bsikar/ra8p1-ereader-kicad/design/core_bulk_c9.md

# C9 core-regulator bulk capacitor

CORE-C9-001, 2026-09-27. C9 remains 47uF on MCU_VCORE with
Procurement_Status HOLD. A candidate is now recorded in its native KiCad
Selection_Basis and Sourcing_Snapshot fields. It is not yet promoted to
the canonical manufacturer part number or purchase BOM.

Candidate: **Murata GRM32ER71A476KE15K**. The manufacturer's
[GRM32ER71A476KE15-04CA reference sheet, January 10, 2025](https://search.murata.co.jp/Ceramy/image/img/A01X/G101/ENG/GRM32ER71A476KE15-04CA.pdf)
specifies 47uF +/-10%, 10V, X7R, -55..125C and 1210 size.
Body dimensions are 3.2 +/-0.3 by 2.5 +/-0.2 by 2.5 +/-0.2mm.
K is the 4000-piece reel packaging code; L is the 1000-piece reel code
for this same manufacturer control code. This does not establish electrical
equivalence to the older 6.3V E20 reference component.

[DigiKey candidate page](https://www.digikey.com/en/products/detail/murata-electronics/GRM32ER71A476KE15K/16034240),
observed 2026-09-27: Active, 1595 unreserved, 17-week standard lead time,
USD0.98 at quantity 1 and USD0.43690 at quantity 100. Cut-tape ordering
code is 490-GRM32ER71A476KE15KCT-ND. An earlier search result showed
13123; the opened page's 1595 supersedes that indexed count. Stock and
price are observations, not reservation or manufacturer lifecycle guarantees.

Historical hold: on 2026-09-05 the native field recorded Mouser stock7034
and an End of Life flag for GRM32ER70J476KE20L, conflicting with DigiKey's
indexed Active/zero-stock result. Do not erase this history by presenting
the E15 candidate as a renamed E20 part.

Initial-tolerance arithmetic is 47*(1-0.10)=42.3uF and
47*(1+0.10)=51.7uF. These are measurement-condition endpoints, not
guaranteed effective capacitance at the core voltage. The X7R temperature
classification alone does not establish a combined DC-bias, aging and
temperature bound.

Before final selection, compare manufacturer DC-bias/impedance data against
the actual RA8P1 core-voltage range and the allowed output network in the
Renesas hardware manual. Verify L1, the twelve 220nF local bypasses and C9
as one regulator output network, including startup and transients. A higher
voltage rating by itself is not proof of loop compatibility. Obtain the
applicable manufacturer approval specification before procurement.

This pass changes hidden metadata only; value, connectivity, drawing and
the existing purchase hold remain unchanged. The main-rail inventory must
continue to identify C9's canonical MPN as unspecified until selection is
approved electrically.

## CORE-C9-002: regulator acceptance evidence (2026-10-04)

Re-read RA8P1 HUM R01UH1064EJ0130 Rev.1.30, pages 4042-4044 and
4047, using the manufacturer's downloaded manual. Table 69.2 / Figure
69.1 establish the 2.2uH and 47uF output topology, twelve local 220nF
bypasses, and C9 return to VSS_DCDC. Section 69.3 recommends inductor
DCR at most 100mOhm. These passages do not state a numeric capacitor
ESR window or a minimum effective output capacitance. Do not invent
such limits or treat the nominal 47uF as an effective-capacitance floor.

Table 70.2 gives typical DCDC core targets of 0.950/0.925V in high-speed
mode and 0.950/0.925/0.825/0.765/0.715V in software standby. Its DCDC
rows have no min/max entries. The 0.92..0.99V external-VDD range and
1.2V absolute maximum are not substituted for a DCDC output guarantee.

Murata's [manufacturer product page](https://www.murata.com/en-eu/products/productdetail?partno=GRM32ER71A476KE15L)
identifies E15 L/K packing variants and the same 47uF, 10V X7R family.
This supports candidate identity; it does not establish regulator acceptance.
The previously linked detailed PDF returned HTTP 404 during this check;
no new DC-bias/impedance bound was obtained. C9 remains HOLD with no
canonical purchase MPN. Next evidence needed is current manufacturer
characterization and a Renesas-supported replacement acceptance criterion,
followed by output-network startup/transient validation.

This evidence update changes no CAD or BOM. The saved 14-page PDF and
97-error/11-warning ERC checkpoint remain applicable.
