bsikar/ra8p1-ereader-kicad/design/ereader_requirements.md

# E-reader hardware requirements

**Owner update, 2026-10-05:** PCM768/DSD512, premium Bluetooth audio and the
higher desktop output targets are now required. The authoritative new
[target contract and corrective plan](audio_external_review_2026-10-05.md#owner-adopted-target-contract)
supersedes the older optional-format, 2 W floor / 4 W stretch and 16 Vrms
language below. RA8P1 remains the application/system master. The existing
schematic does not yet implement these requirements; exact components,
continuous thermal capability and codec licenses remain engineering gates.

## Product definition

The owner's 2026-10-04 premium portable/desktop audio requirements are
tracked in [audio Stage 1 requirements](audio_stage1_requirements.md).
Network music comes from the owner's server; hardware resources/interfaces
are in scope, commercial streaming-service integration is not required.
Prior audio part choices remain provisional until the staged study closes.

Design a standalone RA8P1 e-reader using the existing `ereader/` KiCad project.
Integrate the e-paper timing controller, display power supplies, system power
management, and front-light driver on the main PCB. The Waveshare IT8951 HAT
is a prototyping reference, not a module in the finished product.

The following requirements were confirmed on 2026-09-05:

- Renesas RA8P1 host processor. The exact ordering code and package must be
  verified against the manufacturer's documentation before pin assignment.
- Capacitive touch input and physical buttons.
- Front light with independently adjustable warm and cool channels.
- A complete schematic and PCB design, developed and checked section by
  section, followed by whole-board integration and manufacturing checks.
- E-reader scope only. The Gaggia controller is a separate future project.

The active milestone is the complete electrical schematic, including readable
hierarchical sheets, qualified symbol pin mappings, ERC review, and a full
schematic PDF. PCB layout, footprint qualification, manufacturing outputs,
and physical bring-up are deferred; they are not schematic acceptance gates.

## Consolidated owner requirements (2026-09-07)

These requirements extend the original e-reader definition; they are not
optional substitutes for the display, touch, or front light. This is also a
portable music player. Unchecked items below are required work, not claims
that the current schematic implements them.

- [ ] RA8P1 host and ESP32-C6 radio, with complete supply, clock, reset,
  boot, programming, interconnect, and powered-off isolation circuits.
- [ ] Integrated e-paper controller, panel high-voltage power and VCOM,
  capacitive touch, and independently adjustable warm/cool front light.
  The Waveshare driver board is for prototyping only.
- [ ] Rechargeable battery, USB-C, charging and power-path management,
  protection, fuel measurement, safe power sequencing, and discharge.
- [ ] External RAM and soldered onboard storage at least matching the
  EK-RA8P1 baseline. The current reference is 64 MiB SDRAM and 64 MiB NOR;
  capacity alone does not establish equivalent bandwidth or compatibility.
- [ ] microSD for local music/files, with exact host interface, voltage,
  card-detect, protection, and repository-example compatibility checked.
- [ ] Premium headphone audio with both 3.5 mm single-ended and 4.4 mm
  balanced outputs, USB-DAC operation, and local-file playback.
  Define measurable noise, distortion, output impedance, load/power range,
  clocking, protection, and thermal requirements. Universal headphone
  compatibility or an unmeasured "best sound" claim is not acceptance.
- [ ] Built-in speakers and their amplifiers, with safe output selection,
  mute/pop suppression, and a complete battery/thermal budget.
- [ ] Two cameras: front-facing for selfies and possible face authentication,
  and rear-facing for photography. Use separate MIPI CSI-to-VIN and parallel
  CEU paths after complete pinmux, clock, bandwidth and power review.
- [ ] Independently controlled front camera illumination and rear flashlight,
  separate from the warm/cool display front light.
- [ ] Water-resistant product architecture, including USB-C moisture detection
  and wet-port power inhibition, with protection for exposed contacts.
- [ ] Five exposed physical buttons as specified below, plus touch input.
- [ ] Sensors, debug and factory recovery, including recovery when normal
  application firmware is unavailable.

### Owner additions (2026-09-13)

The owner requires two cameras and identified the MCU's two-lane MIPI
CSI-to-VIN path and separate 16-bit-capable parallel CEU as the intended
interfaces. An 8-bit parallel sensor remains possible; the peripheral's
maximum bus width does not specify the required sensor width. Verify actual
package pin availability and system bandwidth before promising concurrent
capture. Preserve all five buttons, premium audio, SDRAM, NOR and microSD
while resolving camera pin conflicts; existing reservations may be revised
only with coordinated interface review.

Provide a front-facing camera for selfies and possible face authentication,
with independently adjustable front-facing illumination, and a rear camera
with flashlight capability. Visible selfie illumination is the current
working basis. Infrared/depth sensing and spoof-resistant authentication
remain an investigation, not an implemented or guaranteed Face ID equivalent.
Define separate continuous torch and pulsed flash current/thermal limits,
hardware default-off behavior, and source transient budgets. These lights
do not replace either warm or cool display-frontlight control.

The rechargeable battery and the previously identified Waveshare-based
e-paper setup remain mandatory. The existing integrated-controller direction
is unchanged: the HAT is the prototype reference. The exact purchased panel
assembly and the ED060KHE candidate must not be treated as interchangeable
without matching electrical, touch, light-guide and waveform evidence.

Water resistance is a product requirement even while enclosure and PCB
implementation are deferred. Select connectors and electrical protection
with a sealable enclosure, exposed-contact corrosion and liquid ingress in
mind. USB-C requires moisture detection and a hardware-enforced safe state
that inhibits charging and VBUS sourcing while wet, with a defined dry-port
recovery policy. Review detection coverage, false indications, leakage,
power-off behavior, externally supplied VBUS, and interaction with CC/PD,
USB data and accessory functions before selecting the port controller and
switches. Moisture detection alone does not protect every exposed contact.
Include both headphone jacks, buttons and camera/service interfaces in the
ingress and corrosion review while retaining their required functionality.
No IP rating or immersion tolerance is claimed without an enclosure-level
test definition and physical qualification; water resistance is not an
electrical permission to operate or charge a wet connector.

### Five exposed buttons and recovery contract

The owner specified five buttons total on 2026-09-07. Allocate them as:

| Control | Required role |
| --- | --- |
| Power/wake | Power-on from off; wake/sleep request; orderly shutdown request; firmware-independent held-button forced off/recovery |
| Previous page | Page backward |
| Next page | Page forward |
| Volume down | Decrease audio volume |
| Volume up | Increase audio volume |

This count is one power button, two page buttons, and two dedicated volume
buttons. Do not silently collapse the latter four into two dual-use buttons.
Firmware may add contextual mappings, but the five physical controls remain.
For each, define debounce, ESD, pull defaults, voltage domain, leakage,
simultaneous-key behavior, and operation in off/boot/run/sleep/fault/update.
Reserve real MCU pins and verify wake-capable pin selection against the
selected sleep mode before completing the sheet.

The power button consolidates user-facing power/reset/recovery interaction;
it does not directly short both processors' unrelated boot-mode nets.
Normal startup is hardware controlled. A short press while powered is a
firmware input; a sustained press must ultimately force power off without
working firmware. Release and press again to restart. The exact forced-off
time, rail discharge, brownout/rearm behavior, and deep-sleep wake path require
electrical closure; a nominal timing calculation is not a guaranteed bound.

RA8P1 reset/boot and ESP32 boot service-pad pairs are internal fixture access,
not additional exposed buttons or fitted switches. Keep SWD and documented
ROM-loader access for blank/corrupt firmware. Any optional user-facing
button chord for a recovery UI is a separate firmware contract; do not claim
it substitutes for a proven hardware programming path.

### Execution and acceptance plan

Track the work in epic #821 and subsystem issues #822-#834, #840 (audio),
and #841 (camera). Issues #835-#838 cover deferred PCB/manufacturing stages.
Power and controls are shared work under #825/#832; memory, onboard storage
and microSD are under #827. Reopen interface and power-budget decisions when
the expanded audio/camera load invalidates earlier allocations.

1. Complete and independently review each electrical section and its exact
   symbol pin mapping; keep the BOM synchronized with placed parts.
2. Select viable parts using primary datasheets and dated DigiKey/Mouser
   stock, price, lifecycle, and performance evidence. Flag unqualified
   candidates and unavailable supporting specifications explicitly.
3. Connect hierarchical interfaces and actual MCU pins, including all rail,
   timing, pinmux, powered-off, recovery, and firmware dependencies.
4. Put useful equations, assumptions, results, and stable calculation IDs
   on the schematic and link them to full engineering documents. Verify
   calculations with Python; distinguish estimates from guaranteed limits.
5. Before each commit/push, review connectivity, pin types, ERC findings,
   calculations, BOM, and the native schematic plus every changed PDF page.
   Existing ERC errors are not a passing full-design gate.
6. Export the full multipage schematic PDF with the export script. Version
   editable project files, local libraries, necessary references, BOM,
   engineering documents, and exports using portable project-relative paths.
7. Complete whole-design review under #834 before claiming schematic done.
   PCB layout and footprint/model qualification remain deferred.

Latest owner direction is native KiCad GUI editing for design work. Scripts
are for exports and permitted supporting calculations/imports, not schematic
generation. Parallel agents research and independently review while one
editor owns the live KiCad design. Maintain compact, consistent symbols,
short clear wiring, readable hierarchy, standard power symbols, and honest
ERC drive semantics; do not add power flags merely to hide real errors.

Supporting engineering documents: [power](system_power_design.md),
[power button](single_button_power.md), [service](service_interface.md),
[audio](audio_subsystem.md), and
[camera/storage/memory](camera_storage_interfaces.md).

### Component selection and procurement acceptance

Owner requirement, October 5, 2026: apply these checks to every placed part
and to every future selection, including passives and purchased modules.

1. Verify the exact ordering code against manufacturer lifecycle information.
   Reject NRND/EOL choices for new design unless the owner explicitly accepts
   an exception. Record PCNs, replacement codes and any published longevity
   commitment with its scope and end date. Active status alone cannot promise
   that a component will not become obsolete soon.
2. Find an authorized, in-stock quantity-one offer. Record supplier, ordering
   code, carrier choice, minimum/multiple, price, stock quantity and evidence
   date/age. Stock must cover the number fitted to one board. Factory reel
   size is not a distributor cut-tape minimum; avoid optional reeling fees.
   Cached stock, backorder prices and failed page retrievals cannot pass a
   live procurement check.
3. Justify electrical fit for each use and compare realistic alternatives.
   Include voltage/current/temperature limits, timing, noise, tolerances,
   startup, shutdown, partial-power behavior and fault conditions as relevant.
   Matching pin numbers or a distributor's substitute label does not qualify
   a replacement circuit.
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
