bsikar/ra8p1-ereader-kicad/resources/manuals/Renesas_EK-RA8D2_Board_BOM.xlsx

 |  | Bill of Materials
 |  | d019762
 | Document Number | d019762_02
 | Project Name | EK-RA8D2
 | Variant | customer
 | Version | 0303
 | Date | 18/11/2025
Line # | Part Number | Value | Designator | Description | Quantity | Fitted | Remarks | Manufacturer | Manufacturer Part Number
 | ACS-00000005 |  | ACS5, ACS6, ACS7, ACS8 | Pan Phillips Screw, M3x0p5, Length 6mm, Natural, Nylon | 4 | Fitted |  | Essentra | 50M030050P006
 | ICS-00000034 |  | U6, U9, U19 | Bus Driver, 4-Func, 1-Bit, True Output, CMOS, DHVQN14, SOT762-1 | 3 | Fitted |  | Nexperia | 74CBTLV3126BQ,115
 | ICS-00000017 |  | U5, U12, U13, U22, U23, U24, U25 | Octal FET Bus Switch, 5 ohm, 0.3ns max delay, DHVQFN20 | 7 | Fitted |  | Nexperia | 74CBTLV3245BQ-Q10X
 | MIS-00003478 | TP | TP1, TP2, TP3, TP4, TP7, TP8, TP9, TP10 | Testpoint Miniature SMD 3.81mmx2.03mm | 8 | Fitted |  | Keystone | 5019
 | CON-00000063 |  | J41 | Header,4way,2row,vertical,2mm,SMD | 1 | Fitted |  | Amphenol Communications Solutions | 57202-G52-02ALF
 | CON-00000093 |  | J1 | Header,40way,2row,vertical,2.54mm,SMT | 1 | Fitted |  | Amphenol Communications Solutions | 95157-240LF
 | DIO-00000012 |  | LED1 | Standard LEDs - SMD Blue, 470nm 90 to 145 mcd | 1 | Fitted |  | Wurth Elektronik | 150060BS75000
 | DIO-00000013 |  | LED2 | Standard LEDs - SMD Green, 525nm 220 to 430 mcd | 1 | Fitted |  | Wurth Elektronik | 150060GS75000
 | DIO-00000014 |  | LED3 | Standard LEDs - SMD Red, 625nm 120 to 250 mcd | 1 | Fitted |  | Wurth Elektronik | 150060RS75000
 | DIO-00000015 |  | LED5, LED7 | Standard LEDs - SMD Yellow, 590nm 90 to 120 mcd | 2 | Fitted |  | Wurth Elektronik | 150060YS75000
 | CON-00000066 |  | J35 | FFC/FPC Connector, 40 Contact(s), 1 Row(s), Female, Right Angle, 0.019 inch Pitch, Surface Mount Terminal, Locking, Beige Insulator | 1 | Fitted |  | Molex | 505110-4091
 | CON-00000097 |  | J6, J8, J9, J16 | Header, 3way, 1row, vertical, 2.00mm, SMD | 4 | Fitted |  | TE Connectivity | 2842102-3
 | CON-00000065 |  | J7, J10, J11 | Connector USB 3.2 Gen2 Type C Horizontal SMD | 3 | Fitted |  | Amphenol Commercial | 12401610E4#2A
 | CON-00000062 |  | J27, J28 | Grove Header,4Way,1 Row, Horizontal,2mm,THT | 0 | Not Fitted |  | Seeed Studio | 110990037
 | CON-00000088 |  | J15 | 10/100/1000 Ethernet Jack, RJ45, Right Angle SMT, No LEDs | 1 | Fitted |  | Wurth Elektronik | 7498111001A
 | CON-00003283 |  | J33, J34, J36, J60 | Header,2way,1row,vertical,2.54mm,THT | 0 | Not Fitted |  | Wurth Elektronik | 61300211121
 | CON-00003286 |  | J31 | Header,5way,1row,vertical,2.54mm,THT | 0 | Not Fitted |  | Wurth Elektronik | 61300511121
 | CON-00003301 |  | J4, J17 | Header,20way,2row,vertical,2.54mm,THT | 0 | Not Fitted |  | Wurth Elektronik | 61302021121
 | CON-00003310 |  | J2, J3 | Header,40way,2row,vertical,2.54mm,THT | 0 | Not Fitted |  | Wurth Elektronik | 61304021121
 | CON-00000115 |  | J38 | Header,20way,2row,vertical,2.00mm,THT | 0 | Not Fitted |  | Wurth Elektronik | 62002021121
 | MEC-00003402 |  | SW4 | WS-DISV Small Compact SMT Flat Actuator with Top Tape 1.27 mm | 1 | Fitted |  | Wurth Elektronik | 416131160808
 | CRY-00000004 | 32.768kHz | X2 | Crystal, 32.768kHz, 12.5pF, 3.2x1.5 | 1 | Fitted |  | Abracon | ABS07-32.768KHZ-1-T
 | DIO-00000007 |  | D3, D4, D6, D14 | Rectifier Diode, Schottky, 1 Phase, 1 Element, 3A, 40V V(RRM), Silicon | 4 | Fitted |  | Diodes Inc. | B340AQ-13-F
 | IND-00000002 | 4.7µH | L1 | Power Inductor Shielded Multilayer 4.7uH 20% 3MHz Ferrite 700mA | 1 | Fitted |  | Pulse Electronics | BKPB002012104R7MA2
 | CAP-00003477 | 27pF | C22, C23 | Capacitor,EIA0402,27p,50V,C0G | 2 | Fitted |  | Yageo Group | CC0402JRNPO9BN270
 | CON-00000111 |  | J21, J22 | Socket,8way,1row,vertical,2.54mm,THT | 0 | Not Fitted |  | Samtec | CES-108-01-T-S
 | ICS-00000019 |  | U14 | Ultra-Low Power Stereo Codec | 1 | Fitted |  | Renesas | DA7212-01UM2
 | IND-00000004 | 90 | FL1, FL2 | Common Mode Choke / Filters, 90uH 25%, 0.1A, 3.8Ohm DCR | 2 | Fitted |  | Murata | DLM0NSM900HY2D
 | CRY-00000002 | 12MHz | X3 | Crystal, 12.000MHz, 10 pF, 2.5x2 | 1 | Fitted |  | ECS International | ECS-120-10-36B-CWY-TR
 | CRY-00000003 | 25MHz | X4 | Crystal, 25.000MHz, 10 pF, 2x1.6 | 1 | Fitted |  | ECS International | ECS-250-10-37B-CTN-TR
 | CON-00003434 |  | J32 | Edge Rate Rugged High Speed Socket/Terminal Strip | 1 | Fitted |  | Samtec | ERF8-013-05.0-L-DV-TR
 | RES-00003205 | 10m | R7, R98 | Resistor,EIA0603,10m,0.25W | 2 | Fitted |  | Panasonic | ERJ-3LWFR010V
 | RES-00003215 | 1k | RA21 | Array/Network Resistor, Isolated, Metal Glaze/thick Film, 0.063W, 1000ohm, 25V, 5% +/-Tol, 200ppm/Cel, Surface Mount, 1506 | 1 | Fitted |  | Panasonic | EXB-2HV102JV
 | RES-00003208 | 10k | RA1, RA20 | Resistor Network & Array,EIA1506,10k,0.063W | 2 | Fitted |  | Panasonic | EXB-2HV103JV
 | CRY-00000005 | 24MHz | X1 | Crystal, 24MHz, 10pF, 3.2x2.5 | 1 | Fitted |  | Diodes Inc. | FL2400022
 | CON-00000113 |  | J13 | Header,10way,2row,vertical,1.27mm,SMD | 1 | Fitted |  | Samtec | FTSH-105-01-F-DV-K-TR
 | CON-00000114 |  | J20 | Header,20way,2row,vertical,1.27mm,SMD,gold flash on post | 1 | Fitted |  | Samtec | FTSH-110-01-F-DV-K-TR
 | CAP-00000010 | 100nF | C128, C129 | Capacitor,EIA1206,100n,100V,C0G | 2 | Fitted |  | Murata | GCM31C5C2A104JE02L
 | CAP-00003207 | 22µF | C82 | Capacitor,EIA1206,22u,10V,X7R | 1 | Fitted |  | Murata | GCM31CR71A226KE02L
 | CAP-00003208 | 220nF | C50, C52, C53, C54, C55, C58, C59, C63, C73, C74, C75, C76, C99 | Capacitor,EIA0402,220n,16V,X7R | 13 | Fitted |  | Murata | GCM155R71C224KE02D
 | CAP-00003212 | 10nF | C29, C87, C89, C92, C97, C98, C101, C102, C103, C104, C105 | Capacitor,EIA0402,10n,50V,X7R | 11 | Fitted |  | Murata | GCM155R71H103KA55D
 | CAP-00000002 | 330pF | C142 | Capacitor,EIA0402,330p,100V,X7R | 1 | Fitted |  | Murata | GCM155R72A331KA37D
 | CAP-00000012 | 15pF | C21, C24 | Capacitor,EIA0201,15p,50V,C0G | 2 | Fitted |  | Murata | GCM0335C1H150FA16D
 | CAP-00003371 | 47µF | C77 | Capacitor,EIA1206,47u,6.3V,X7U | 1 | Fitted |  | Murata | GRM31CE70J476ME15L
 | CAP-00003447 | 10µF | C20, C34, C64, C65, C79, C88, C90, C100, C106, C115, C149 | Capacitor,EIA0402,10u,10V,X5R | 11 | Fitted |  | Murata | GRM155R61A106ME11D
 | CAP-00003447 | 10µF | C162 | Capacitor,EIA0402,10u,10V,X5R | 0 | Not Fitted |  | Murata | GRM155R61A106ME11D
 | CAP-00000013 | 22µF | C141 | Capacitor,EIA0402,22u,10V,X5R | 1 | Fitted |  | Murata | GRM158R61A226ME15D
 | CAP-00000011 | 1µF | C130, C131, C132, C133, C134, C135, C136, C137, C138 | Capacitor,EA0201,1u,10V,X6S | 9 | Fitted |  | Murata | GRT033C81A105ME13D
 | CAP-00000011 | 1µF | C143, C144, C145, C146, C147 | Capacitor,EA0201,1u,10V,X6S | 0 | Not Fitted |  | Murata | GRT033C81A105ME13D
 | CAP-00000015 | 2.2µF | C10, C83 | Capacitor,EIA0402,2.2u,16V,X6S | 2 | Fitted |  | Murata | GRT155C81C225KE13D
 | CAP-00000014 | 1µF | C18, C30, C60, C66, C110, C114, C152, C154 | Capacitor,EIA0402,1u,25V,X6S | 8 | Fitted |  | Murata | GRT155C81E105KE13D
 | CAP-00003217 | 470nF | C68 | Capacitor,EIA0402,470n,10V,X7R | 1 | Fitted |  | Murata | GRT155R71A474KE01D
 | CAP-00003203 | 100nF | C1, C2, C3, C4, C5, C6, C7, C8, C9, C11, C12, C13, C14, C15, C16, C17, C19, C25, C26, C28, C31, C32, C33, C35, C36, C37, C39, C40, C41, C42, C43, C44, C45, C46, C47, C48, C49, C51, C56, C57, C61, C67, C71, C72, C78, C80, C81, C84, C85, C91, C93, C94, C107, C109, C111, C112, C113, C116, C117, C118, C121, C122, C123, C124, C125, C126, C127, C140, C148, C151, C155, C156, C157, C158, C159, C160 | Capacitor,EIA0402,100n,50V,X7R | 76 | Fitted |  | Murata | GRT155R71H104KE01D
 | CAP-00003203 | 100nF | C108, C139 | Capacitor,EIA0402,100n,50V,X7R | 0 | Not Fitted |  | Murata | GRT155R71H104KE01D
 | CAP-00003210 | 4.7µF | C27, C69, C70, C153 | Capacitor,EIA0603,4.7u,16V,X7S | 4 | Fitted |  | Murata | GRT188C71C475KE13D
 | CAP-00003215 | 10pF | C95, C96, C119, C120 | Capacitor,EIA0402,10p,100V,C0G | 4 | Fitted |  | Murata | GRT1555C2A100JA02D
 | CAP-00003209 | 47pF | C62 | Capacitor,EIA0402,47p,100V,C0G | 1 | Fitted |  | Murata | GRT1555C2A470JA02D
 | TRA-00000004 |  | Q10, Q18 | N-Channel 30V 5A 1.3W MOSFET | 2 | Fitted |  | Infineon | IRLML6344TRPBF
 | ICS-00000135 |  | U3 | NOR Flash 512Mb, Octal Flash, 3V, 24-ball TFBGA | 1 | Fitted |  | ISSI | IS25LX512M-JHLE
 | ICS-00000024 |  | U2 | 512Mb Synchronous DRAM, 16MX32, 5.4ns, CMOS, TF-BGA90 | 1 | Fitted |  | ISSI | IS42S32160F-6BLI
 | ICS-00000140 |  | U52 | LDO with Low ISUPPLY, High PSRR 1.8V fixed, 300mA | 1 | Fitted |  | Renesas | ISL9005AIRCZ-T
 | ICS-00000015 |  | U16, U17 | Single, General Purpose Micropower, RRIO Operational Amplifier | 2 | Fitted |  | Renesas | ISL28113FEZ-T7
 | ICS-00000014 |  | U8 | High Performance 3A Linear Regulator | 1 | Fitted |  | Renesas | ISL80103IRAJZ
 | CAP-00000022 | 4.7µF | C38, C150 | Capacitor, EIA0402, 4.7u, 16V, X5R | 2 | Fitted |  | KYOCERA AVX | KGM05CR51C475MH
 | DIO-00003239 |  | LED8 | Standard LEDs - SMD Green, 570nm 2.2 to 5.6 mcd | 1 | Fitted |  | Osram | LGL29K-G2J1-24
 | DIO-00003241 |  | LED6 | Standard LEDs - SMD Orange, 606nm 3.55 to 14 mcd | 1 | Fitted |  | Osram Opto | LOL29K-H2L1-24
 | DIO-00000002 |  | LED4 | Standard LEDs, SMD Ultra Bright White | 1 | Fitted |  | Lite-On | LTW-C191DS5
 | IND-00000008 | 120 | L5 | Ferrite Chip, 1.2A, 90mOhm DCR, 120Ohm Impedance @100MHz | 1 | Fitted |  | TDK | MPZ1005S121CT000
 | ACS-00000000 |  | ACS1, ACS2, ACS3, ACS4 | Female Standoff; Nylon; Natural; M3; 14.0 mm Spacer | 4 | Fitted |  | Essentra | MTS-14
 | RES-00000000 | 100k | RT1, RT2 | NTC Thermistor, R_EIA0402, 100K, 4250K | 2 | Fitted |  | Murata | NCP15WF104F03RC
 | CON-00000043 |  | J19 | Socket, 6way, 1 Row, Vertical, 2.54mm, SMD | 1 | Fitted |  | Sullins | NPTC061KFXC-RC
 | CON-00000044 |  | J18, J23 | Socket, 8way, 1 Row, Vertical, 2.54mm, SMD | 2 | Fitted |  | Sullins | NPTC081KFXC-RC
 | CON-00000045 |  | J24 | Socket, 10way, 1 Row, Vertical, 2.54mm, SMD | 1 | Fitted |  | Sullins | NPTC101KFXC-RC
 | CON-00000078 |  | J5 | Header, 2way, 1row, vertical, 2.00mm, THT | 0 | Not Fitted |  | Sullins | NRPN021PAEN-RC
 | CON-00000079 |  | J12 | Header, 3way, 1row, vertical, 2.00mm, THT | 0 | Not Fitted |  | Sullins | NRPN031PAEN-RC
 | CON-00000105 |  | J29 | Header, 8way, 2row, vertical, 2.0mm, SMD | 1 | Fitted |  | Sullins | NRPN042MAMS-RC
 | CON-00000094 |  | J14, J37 | Header,26way,2row,vertical,2.00mm,THT | 0 | Not Fitted |  | Sullins | NRPN132PAEN-RC
 | ICS-00000025 |  | U11 | Ethernet Network Connection GPY111 Gigabit Ethernet (GbE) | 1 | Fitted |  | MaxLinear | PEF7071VV16-LLHU
 | ICS-00000012 |  | U15 | Low-voltage translating 8-bit I2C-bus I/O Expander | 1 | Fitted |  | Diodes Inc. | PI4IOE5V6408ZTAEX
 | RES-00003207 | 5m | R2, R3 | Current Sense Resistor,EIA0612,5m,1W | 2 | Fitted |  | Yageo Group | PS0612FKE070R005L
 | MEC-00000000 |  | SW3 | SMD Push Button Switch, 4-pin, 6x6mm, 4.3mm height, Red Actuator | 1 | Fitted |  | C&K Components | PTS645SK43SMTR92LFS
 | MEC-00000002 |  | SW1, SW2 | SMD Push Button Switch, 4-pin, 6x6mm, 4.3mm height, Blue Actuator | 2 | Fitted |  | C&K Components | PTS645SM43SMTR92LFS
 | ICS-00000006 |  | U7 | Renesas RA4M2 32-bit MCU, ARM Cortex-M33, 100MHz, 512kB Flash, 128 kB RAM, 48-pin LQFP package (used for J-Link onboard debug i/f) | 1 | Fitted |  | Renesas | R7FA4M2AD3CFL#AA0
 | ICS-00000098 |  | U1 | Renesas RA8D2 32-bit MCU, High-performance 1 GHz Arm® Cortex®-M85 core, 250 MHz Arm® Cortex®-M33 core, up to 1 MB code MRAM, and 2 MB SRAM with ECC | 1 | Fitted |  | Renesas | R7KA8D2KFLCAC
 | ICS-00000018 |  | U4, U18 | USB Power Delivery Controller, USB 3.1, HVQFN32 | 2 | Fitted |  | Renesas | R9A02G011GNP#AC0
 | DIO-00000005 |  | D15, D16 | Rectifier Diode, Schottky, 1 Phase, 1 Element, 1A, 40V V(RRM), Silicon | 2 | Fitted |  | ROHM | RB168MM-40TFTR
 | RES-00000882 | 1.5k | R37 | Resistor,EIA0402,1.5k,0.0625W | 1 | Fitted |  | Yageo Group | RC0402FR-071K5L
 | RES-00000878 | 1k | R24, R88, R122 | Resistor,EIA0402,1k,0.0625W | 3 | Fitted |  | Yageo Group | RC0402FR-071KL
 | RES-00001614 | 2.37k | R33, R34 | Resistor,EIA0402,2.37k,0.0625W | 2 | Fitted |  | Yageo Group | RC0402FR-072K37L
 | RES-00000886 | 2.2k | R80 | Resistor,EIA0402,2.2k,0.0625W | 1 | Fitted |  | Yageo Group | RC0402FR-072K2L
 | RES-00001635 | 3.92k | R41 | Resistor,EIA0402,3.92k,0.0625W | 1 | Fitted |  | Yageo Group | RC0402FR-073K92L
 | RES-00000894 | 4.7k | R11, R25, R26, R28, R38, R44, R54, R56, R83, R103, R109, R111 | Resistor,EIA0402,4.7k,0.0625W | 12 | Fitted |  | Yageo Group | RC0402FR-074K7L
 | RES-00001375 | 4.99 | R112 | Resistor,EIA0402,4.99,0.0625W | 1 | Fitted |  | Yageo Group | RC0402FR-074R99L
 | RES-00000895 | 5.1k | R12, R17, R48, R49, R89, R92 | Resistor,EIA0402,5.1k,0.0625W | 6 | Fitted |  | Yageo Group | RC0402FR-075K1L
 | RES-00000902 | 10k | R6, R14, R36, R39, R40, R45, R46, R47, R52, R71, R77, R94, R95, R99, R105, R107, R113, R119, R120, R121, R123, R136, R137, R138, R139 | Resistor,EIA0402,10k,0.0625W | 25 | Fitted |  | Yageo Group | RC0402FR-0710KL
 | RES-00000903 | 11k | R42, R43 | Resistor,EIA0402,11k,0.0625W | 2 | Fitted |  | Yageo Group | RC0402FR-0711KL
 | RES-00000906 | 15k | R4, R18, R76, R79, R90 | Resistor,EIA0402,15k,0.0625W | 5 | Fitted |  | Yageo Group | RC0402FR-0715KL
 | RES-00000834 | 15 | R1, R114, R115, R116 | Resistor,EIA0402,15,0.0625W | 4 | Fitted |  | Yageo Group | RC0402FR-0715RL
 | RES-00001689 | 16.2k | R8, R85 | Resistor,EIA0402,16.2k,0.0625W | 2 | Fitted |  | Yageo Group | RC0402FR-0716K2L
 | RES-00000907 | 16k | R50, R51 | Resistor,EIA0402,16k,0.0625W | 2 | Fitted |  | Yageo Group | RC0402FR-0716KL
 | RES-00000840 | 27 | R21, R22 | Resistor,EIA0402,27,0.0625W | 2 | Fitted |  | Yageo Group | RC0402FR-0727RL
 | RES-00000913 | 30k | R5, R15, R81, R91 | Resistor,EIA0402,30k,0.0625W | 4 | Fitted |  | Yageo Group | RC0402FR-0730KL
 | RES-00000842 | 33 | R59, R60, R61, R62, R63, R64 | Resistor,EIA0402,33,0.0625W | 6 | Fitted |  | Yageo Group | RC0402FR-0733RL
 | RES-00000843 | 36 | R125, R126 | Resistor,EIA0402,36,0.0625W | 2 | Fitted |  | Yageo Group | RC0402FR-0736RL
 | RES-00000918 | 47k | R31, R82, R102 | Resistor,EIA0402,47k,0.0625W | 3 | Fitted |  | Yageo Group | RC0402FR-0747KL
 | RES-00000926 | 100k | R10, R16, R55, R57, R69, R73, R84, R96, R97, R101, R104, R106, R110 | Resistor,EIA0402,100k,0.0625W | 13 | Fitted |  | Yageo Group | RC0402FR-07100KL
 | RES-00000855 | 110 | R32 | Resistor,EIA0402,110,0.0625W | 1 | Fitted |  | Yageo Group | RC0402FR-07110RL
 | RES-00000858 | 150 | R117, R118, R140 | Resistor,EIA0402,150,0.0625W | 3 | Fitted |  | Yageo Group | RC0402FR-07150RL
 | RES-00000867 | 360 | R124 | Resistor,EIA0402,360,0.0625W | 1 | Fitted |  | Yageo Group | RC0402FR-07360RL
 | RES-00000870 | 470 | R30, R35, R65 | Resistor,EIA0402,470,0.0625W | 3 | Fitted |  | Yageo Group | RC0402FR-07470RL
 | RES-00000801 | 0 | R13, R19, R20, R53, R67, R68, R78, R127, R128, R129, R130, R131, R132, R133, R134, R135 | Resistor,EIA0402,0,0.0625W | 16 | Fitted |  | Yageo Group | RC0402JR-070RL
 | RES-00000801 | 0 | R23, R66, R70, R74, R75, R87, R108 | Resistor,EIA0402,0,0.0625W | 0 | Not Fitted |  | Yageo Group | RC0402JR-070RL
 | RES-00002248 | 2.61k | R29 | Resistor,EIA0603,2.61k,0.1W | 1 | Fitted |  | Yageo Group | RC0603FR-072K61L
 | RES-00002182 | 464 | R27 | Resistor,EIA0603,464,0.1W | 1 | Fitted |  | Yageo Group | RC0603FR-07464RL
 | RES-00000804 | 0 | R9, R58, R86, R93 | Resistor,EIA1206,0,0.25W | 4 | Fitted |  | Yageo Group | RC1206JR-070RL
 | DIO-00003463 |  | D1, D2, D7, D8, D10, D11 | Low Capacitance TVS Diode Array | 6 | Fitted |  | Semtech | RCLAMP0582N.TCT
 | TRA-00000001 |  | Q2, Q3, Q4, Q12, Q21 | N-Channel 60V 250mA Small Signal MOSFET | 5 | Fitted |  | ROHM | RE1L002SNTL
 | RES-00003204 | 220 | R72, R100 | Resistor,EIA2512,220,1W | 2 | Fitted |  | Stackpole Electronics | RMCF2512FT220R
 | TRA-00000003 |  | Q1, Q11 | Dual P-Channel -12V -4.5A MOSFET | 2 | Fitted |  | Vishay | SIA975DJ-T1-GE3
 | ICS-00000194 |  | U10 | Renesas GreenPak PMOD mode controller | 1 | Fitted |  | Renesas | SLG7RN48896
 | CON-00000061 |  | J30 | Wire-to-Board Header,4way, Single Row, Right-Angle, SMD | 0 | Not Fitted |  | JST | SM04B-SRSS-TB(LF)(SN)
 | CON-00000060 |  | J25, J26 | Socket,12way,2row,horizontal,2.54mm,SMD,PMOD_Interface | 2 | Fitted |  | Samtec | SMH-106-02-L-D
 | ICS-00000021 |  | U20 | 4-Bit 1-of-2 FET Multiplexer/Demultiplexer 2.5-V/3.3-V Low-Voltage High-Bandwidth Bus Switch | 1 | Fitted |  | Texas Instruments | SN74CB3Q3257DBQR
 | ICS-00000023 |  | MIC1, MIC2 | Multimode Digital Bottom Port Silicon Digital Microphone with a single bit PDM output | 2 | Fitted |  | Knowles Acoustics | SPH0690LM4H-1
 | IND-00000003 | 2.2µH | L2 | Inductor, 2.2uH, 20%, 7A, Metal-Core | 1 | Fitted |  | TDK | SPM5020T-2R2M-LR
 | ICS-00000096 |  | U21 | 6-GHz, 5-V, 2: 1 (SPDT) 10-channel MIPI switch with 1.8-V logic support 36-NFBGA -40 to 85 | 1 | Fitted |  | Texas Instruments | TMUX646NZECR
 | DIO-00000001 |  | D5, D9, D12 | ESD Suppressor Diode TVS Uni-Dir 22V 55Vc Automotive 2-Pin SGP T/R | 3 | Fitted |  | Semtech | UCLAMP2271P.TNT
 | RES-00003456 | 4.7k | RA2, RA3, RA4, RA5, RA6, RA7, RA8, RA9, RA10 | Resistor Network & Array,0804,4.7k,0.0625W | 9 | Fitted |  | Yageo Group | YC124-FR-074K7L
 | RES-00003206 | 10k | RA11, RA12, RA13 | Resistor Network & Array,0804, 10k,0.0625W | 3 | Fitted |  | Yageo Group | YC124-FR-0710KL
 | RES-00003457 | 33 | RA14, RA15, RA16, RA17, RA18, RA19 | Resistor Network & Array,0804,33,0.0625W | 6 | Fitted |  | Yageo Group | YC124-FR-0733RL
 | RES-00003219 | 50 | RA22, RA23, RA24 | Resistor Network & Array,0804, 50,0.0625W | 3 | Fitted |  | Yageo Group | YC124-FR-0749R9L
