bsikar/ra8p1-ereader-kicad/resources/reference_designs/Renesas_EK-RA8D2_Board_Design_Package/Design Files - Altium/d019762_43_v0303_ek-ra8d2_altium_customer_mp/PCB_Tech_Spec.xlsx

Sheet: Technical data sheet
 | PCB Technology Specification
 |  | Field=DNumber
Field=Dnumber | Document Number | Field=Dnumber_07_S01
Field=ProjectName | Project Name | Field=Proj
 | Variant | Field=VariantName |  | Contact Person |  | Field=Engineer
 | Version | Field=ItemRevision |  | E-Mail |  | Field=Email
 | Date | Field=CurrentDate |  | Telephone |  | Field=Phone
 | General requirements |  |  |  | Production requirements
 | IPC-A-600 |  | Class II |  | PCB-Type |  | Rigid
 | IPC-A-6011/IPC-A-6012 |  | Class II |  | Finished PCB Dimension (mm) |  | 84 mm | x | 190 mm
 | Number of Layers |  | see drawing |  | Create Panel |  | no |  | 5 x 5
 | Conductor min Width / Spacing |  | 60 µm |  | Panel Dimension (mm) |  | 524.8 mm | x | 500 mm
 | Finished Board Thickness |  | 1.40 mm |  | Contour processing |  | Milling
 | Pad finish |  | chem. NI/AU (ENIG) |  | Add tooling holes in panel |  | no
 | Impedance Check |  | yes |  | Inner Thieving Balaning Allowed |  | no
 | E-Test |  | yes |  | Outer Thieving Balancing Allowed |  | no
 | First sample test report |  | no |  | Gold Fingers |  | no
 | Finished copper inside |  | 35µm |  | Edge contact |  | no
 | Finished copper outside |  | 35µm |  | Soldermask Product |  | KSM-6189 BLO3
 |  |  |  |  | Soldermask Color (Top & Bottom ) |  | Renesas Blue CMYK(73,73,0,38 RGB (42,40,157)
 | Materials and Ratings
 | Base Material |  | FR 4
 | Tg (°C min) |  | 170 °C |  | Soldermask finish |  | semi-gloss
 | Td (°C min) |  | 330 °C |  | Silkscreen |  | Top & Bottom
 | RoHS compatible |  | yes |  | Silkscreen Color |  | white
 | UL94V Rating |  | UL94V-0 |  | Silkscreen printing method |  | Silkscreen Printed
 | Drill and Milling |  |  |  | Add additional marking
 | Smallest drill diameter |  | 100 µm |  | Board Lot # |  | no
 | Smallest drill pad |  | 220 µm |  | QC Stamp |  | no
 | Backdrill |  | no |  | UL94V |  | no
 | Blind via |  | no |  | RoHS |  | no
 | Buried via |  | no |  | Manufacturer Logo |  | no
 | Microfill blind via |  | no |  | Date code |  | no
 | Plugging buried via |  | no
 | Via Processing |  | IPC 4761 Type VII |  | Comment
 | Milling tolerance |  | ± 100 µm |  | DNF components are not soldered and so pads for these components must be free from solder. No changes are to made without approval from Renesas. This includes the addition of circuit fiducials but excludes etch compensation. This PCB is not to be marked with UL Logos but processed in a UL Approved process.

Sheet: Data validation
General requirements
IPC-A-600 | IPC-A-6011/IPC-A-6012 | Number of Layers | Pad finish | Impedance Check | E-Test | First sample test report | Finished copper
not applicable | not applicable | see drawing | free | yes | yes | yes | see drawing
Class I | Class I | 2 | HASL lead-free | no | no | no | 18 µm
Class II | Class II | 4 | chem. NI/AU (ENIG) |  | 100% full |  | 35µm
Class III | Class III | 6 | chem. Sn
 |  | 8 | Entek / OSP
 |  | 10 | chem. Silver
 |  | 12
 |  | 14
Materials and Ratings
Base Material | Tg (°C min) | Td (°C min) | RoHS | UL94V
see drawing | see drawing | free | yes | see drawing
FR 4 | 170 °C | see drawing |  | none
Rogers | 150 °C | 330 °C |  | UL94V-0
Polyimid | 180 °C |  |  | UL94V-1
 |  |  |  | UL94V-2 |  |  |  |  |  |  |  |  | Milling tolerance
 |  |  |  |  |  |  |  |  |  |  |  |  | Standard
 |  |  |  |  |  |  |  |  |  |  |  |  | +/- 100 µm
 |  |  |  |  |  |  |  |  |  |  |  |  | +/- 50 µm
Drill and Milling |  |  |  |  |  |  |  |  |  |  |  |  | Production requirements
Backdrill | Blind Via | Buried Via | Microfill blind via | Plugging buried via | Via Processing | Milling Tolerance |  |  |  |  |  |  | rigid
see drawing | no | no | yes | yes | None | not specified |  |  |  |  |  |  | flexibel
yes | yes | yes | no | no | IPC 4761 Type I-a | ± 50 µm |  |  |  |  |  |  | rigid-flex
no | see drawing | see drawing |  |  | IPC 4761 Type I-b | ± 100 µm
 |  |  |  |  | IPC 4761 Type II-a | ± 150 µm
 |  |  |  |  | IPC 4761 Type II-b | ± 200 µm
 |  |  |  |  | IPC 4761 Type III-a | ± 250 µm
 |  |  |  |  | IPC 4761 Type IV-a
 |  |  |  |  | IPC 4761 Type IV-b
 |  |  |  |  | IPC 4761 Type V
 |  |  |  |  | IPC 4761 Type VI-a
 |  |  |  |  | IPC 4761 Type VI-b
 |  |  |  |  | IPC 4761 Type VII
Production requirements
PCB-Type | Create Panel | Contour processing | Add tooling holes in panel | Thieving Balaning Allowed | Gold Fingers | Edge contact | Soldermask Product | Soldermask Color | Soldermask finish | Silkscreen | Silkscreen Color | Silkscreen Printing Method
Rigid | yes | Milling | no | no | yes | yes | free | free | free | none | white | Silkscreen Printed
Flexible | no | V-Scoring | yes, standard | yes, keepaway 2.5mm | no | no | KSM-6189 BLO3 | green | matte | Top |  | Screen
Rigid-Flex |  |  | yes, see drawing |  |  |  |  | blue | semi-gloss | Bottom |  | Direct Print
 |  |  |  |  |  |  |  | Renesas Blue CMYK(73,73,0,38 RGB (42,40,157) |  | Top & Bottom
Add additional marking
no
yes - position free
yes - see drawing
