bsikar/ra8p1-ereader-kicad/resources/reference_designs/Renesas_EK-RA8D2_Board_Design_Package/Manufacturing Files/d019762_07_s07_v0301_ek-ra8d2_pcb_all_layer_mp.pdf

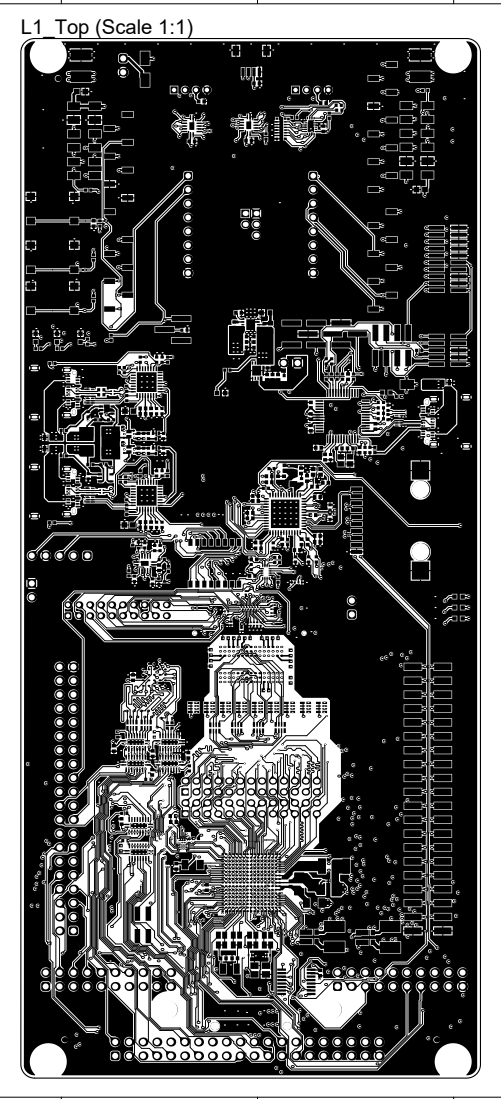
[picture p18: page 1]

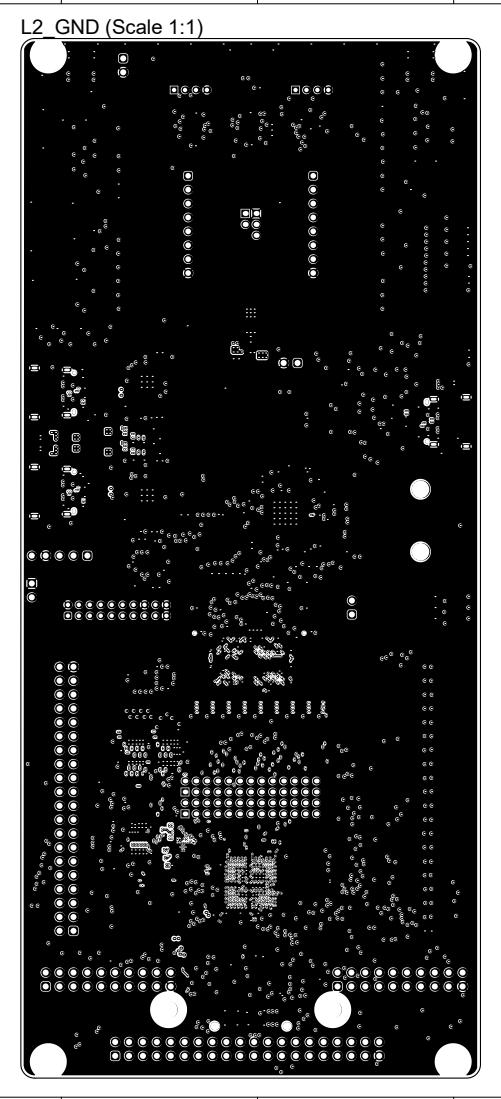
[picture p19: page 2]

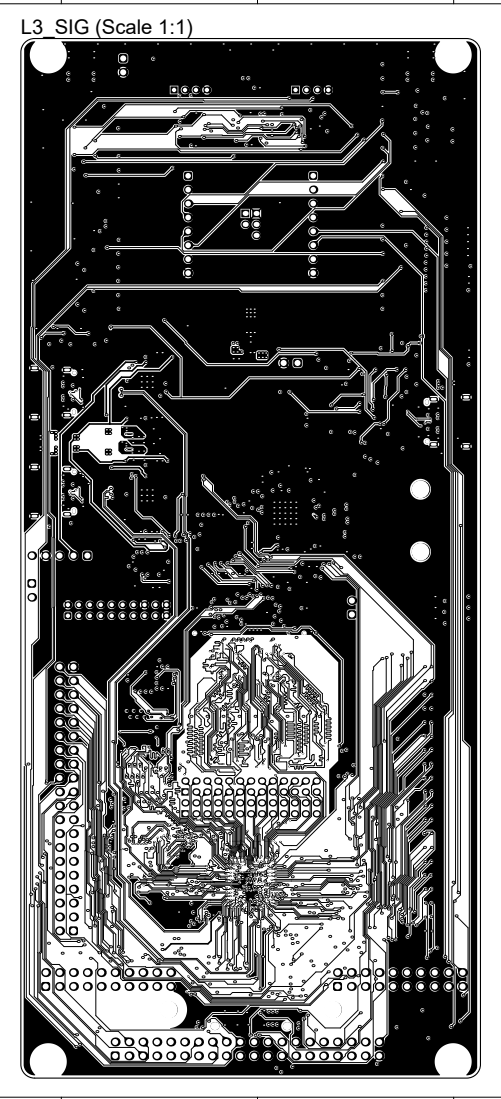
[picture p20: page 3]

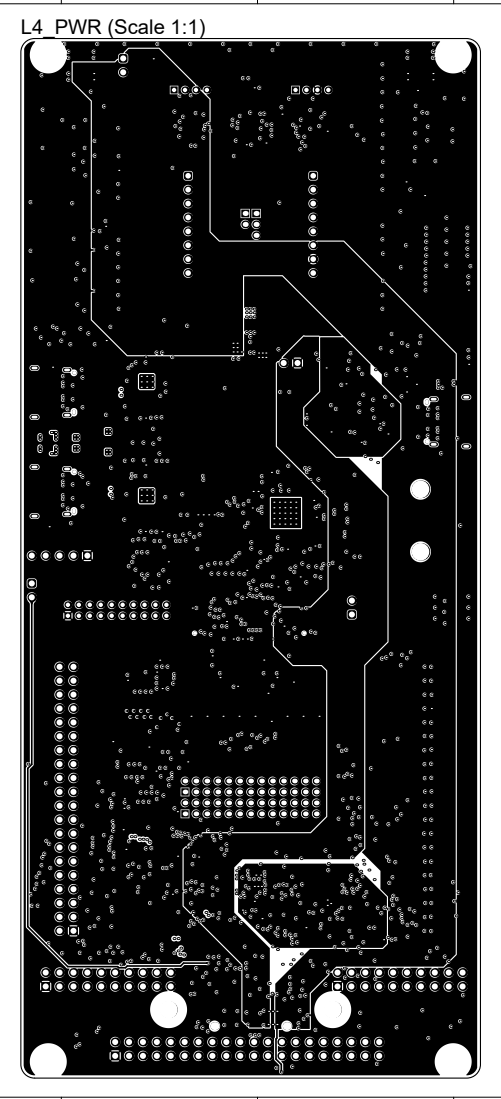
[picture p21: page 4]

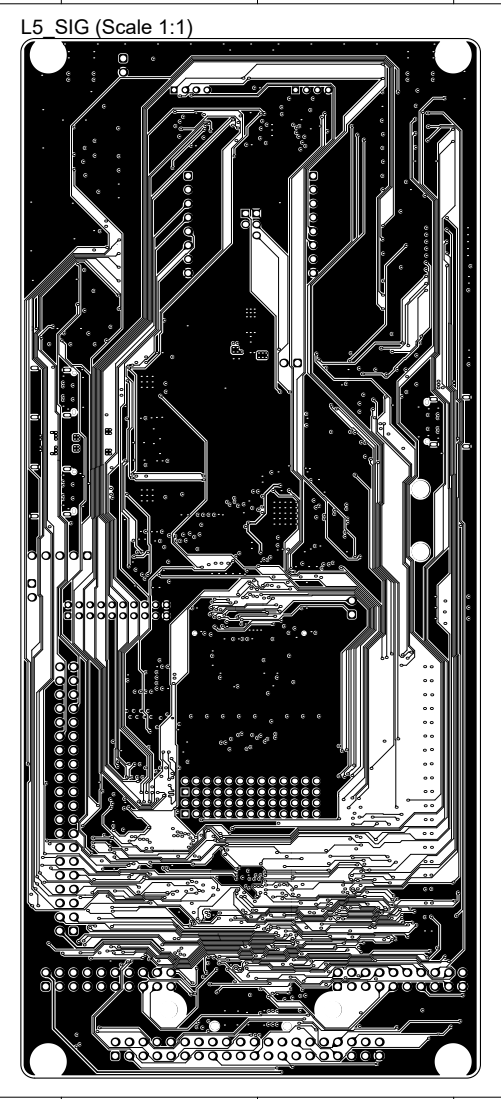
[picture p22: page 5]

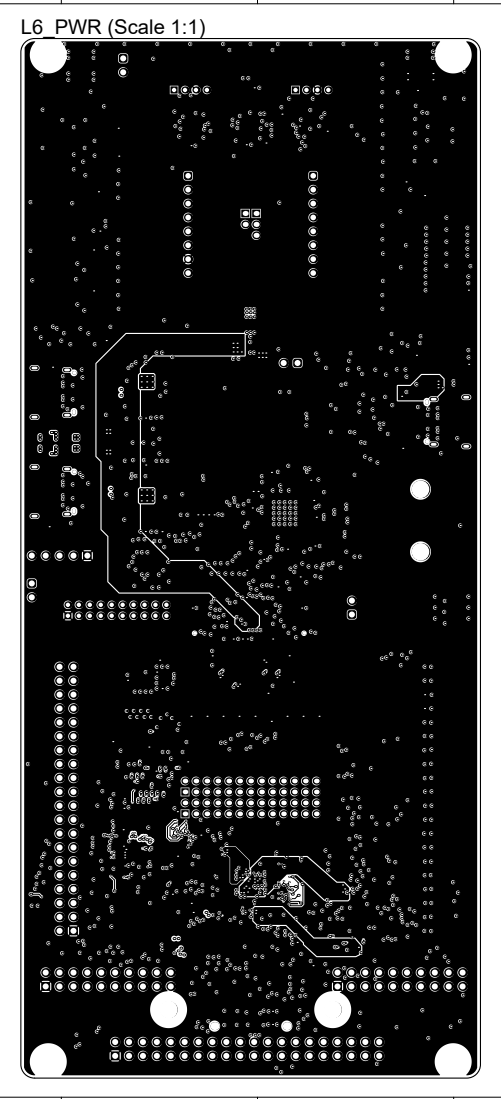
[picture p23: page 6]

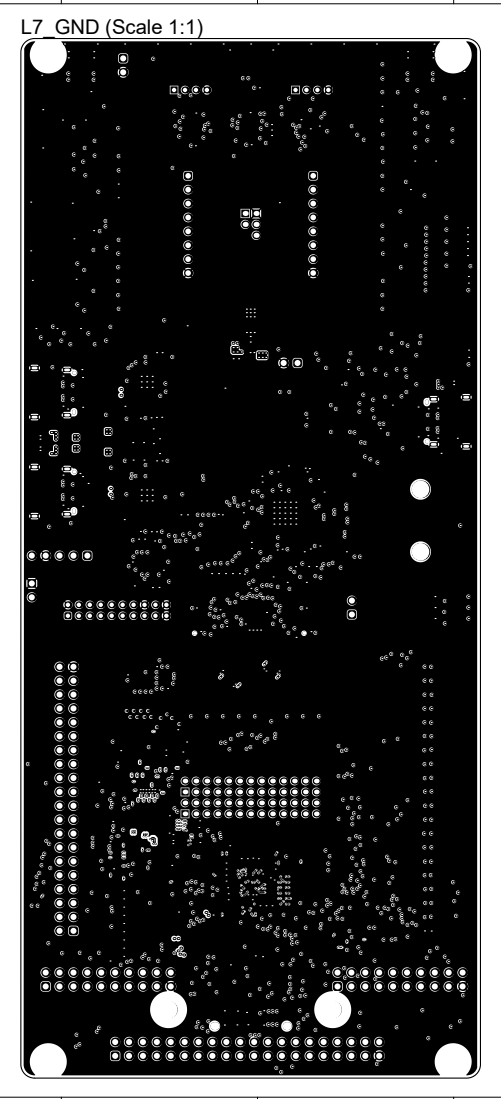
[picture p24: page 7]

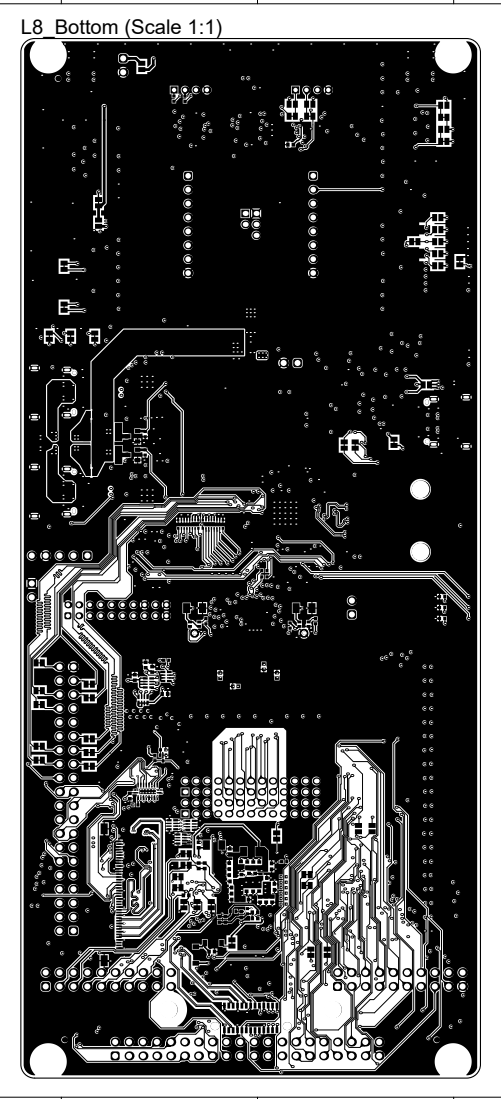
[picture p25: page 8]

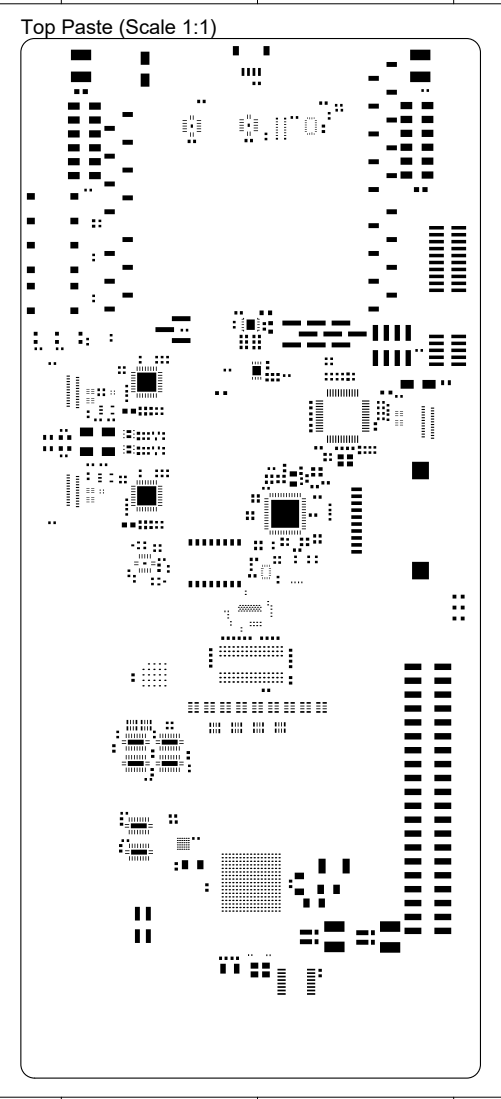
[picture p26: page 9]

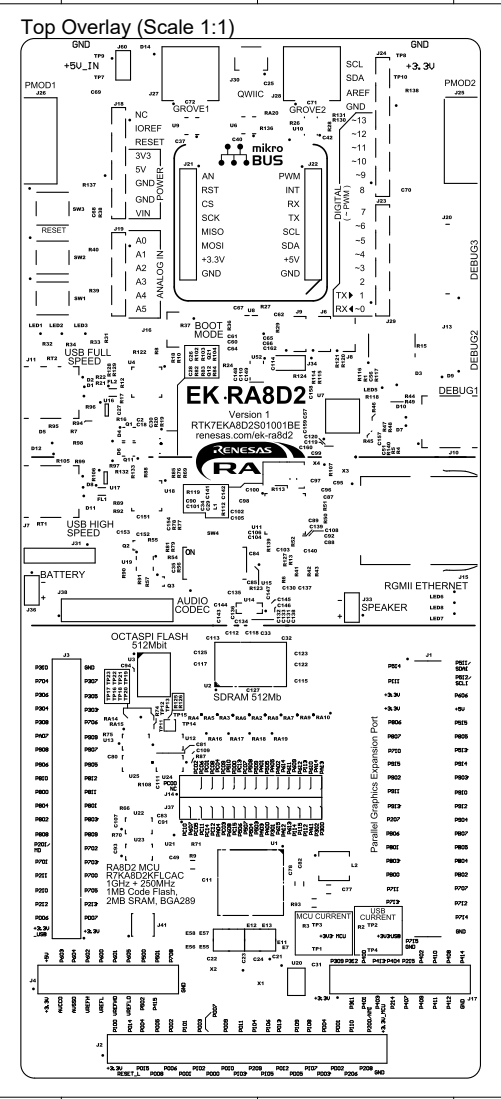
[picture p27: page 10]

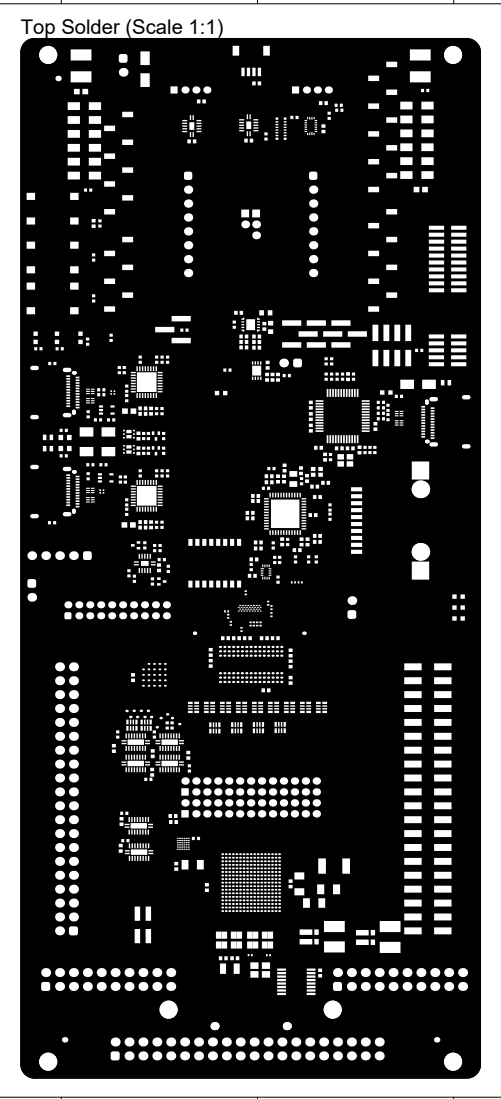
[picture p28: page 11]

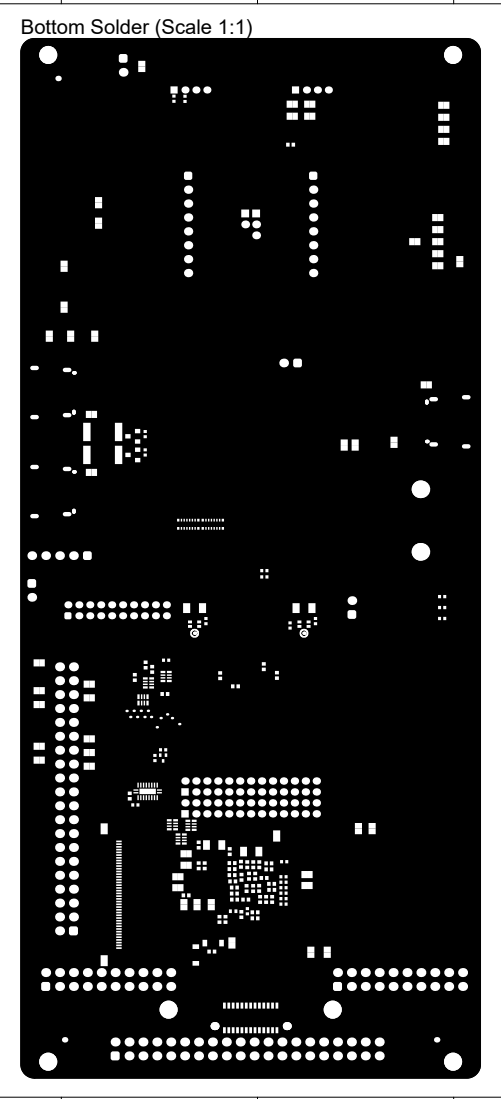
[picture p29: page 12]

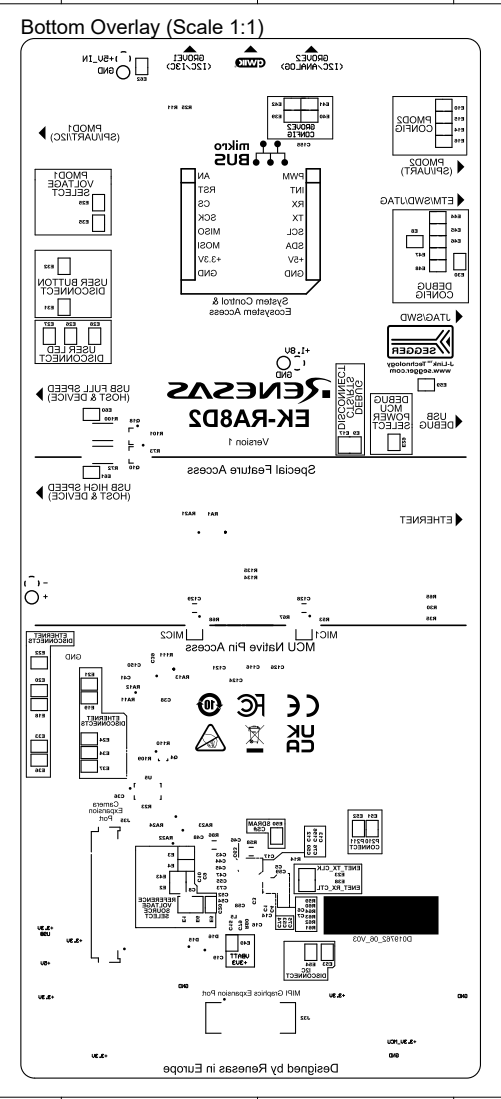
[picture p30: page 13]

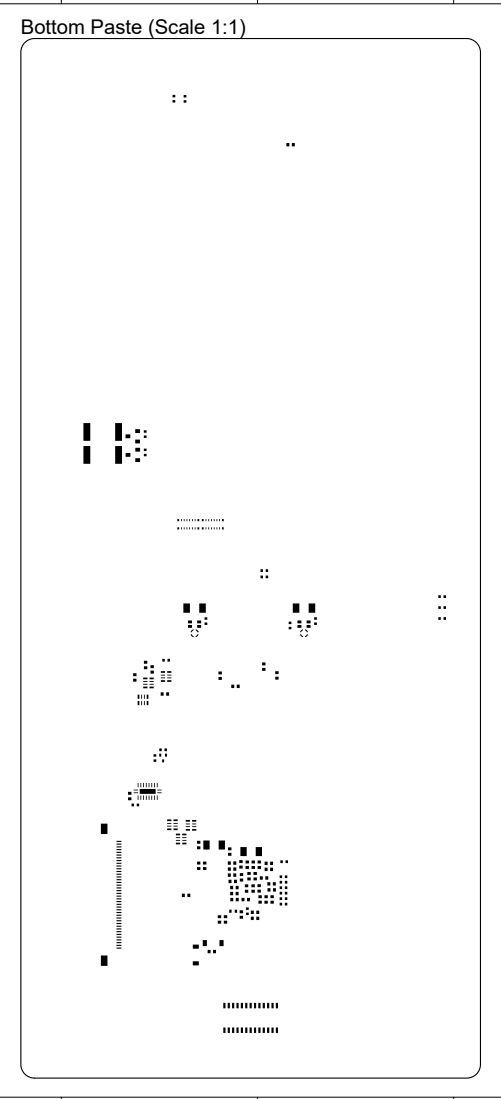
[picture p31: page 14]
