bsikar/ra8p1-ereader-kicad/ereader/mcu_clocks_debug.kicad_sch

## KiCad design ereader/mcu_clocks_debug.kicad_sch (2026-10-07)

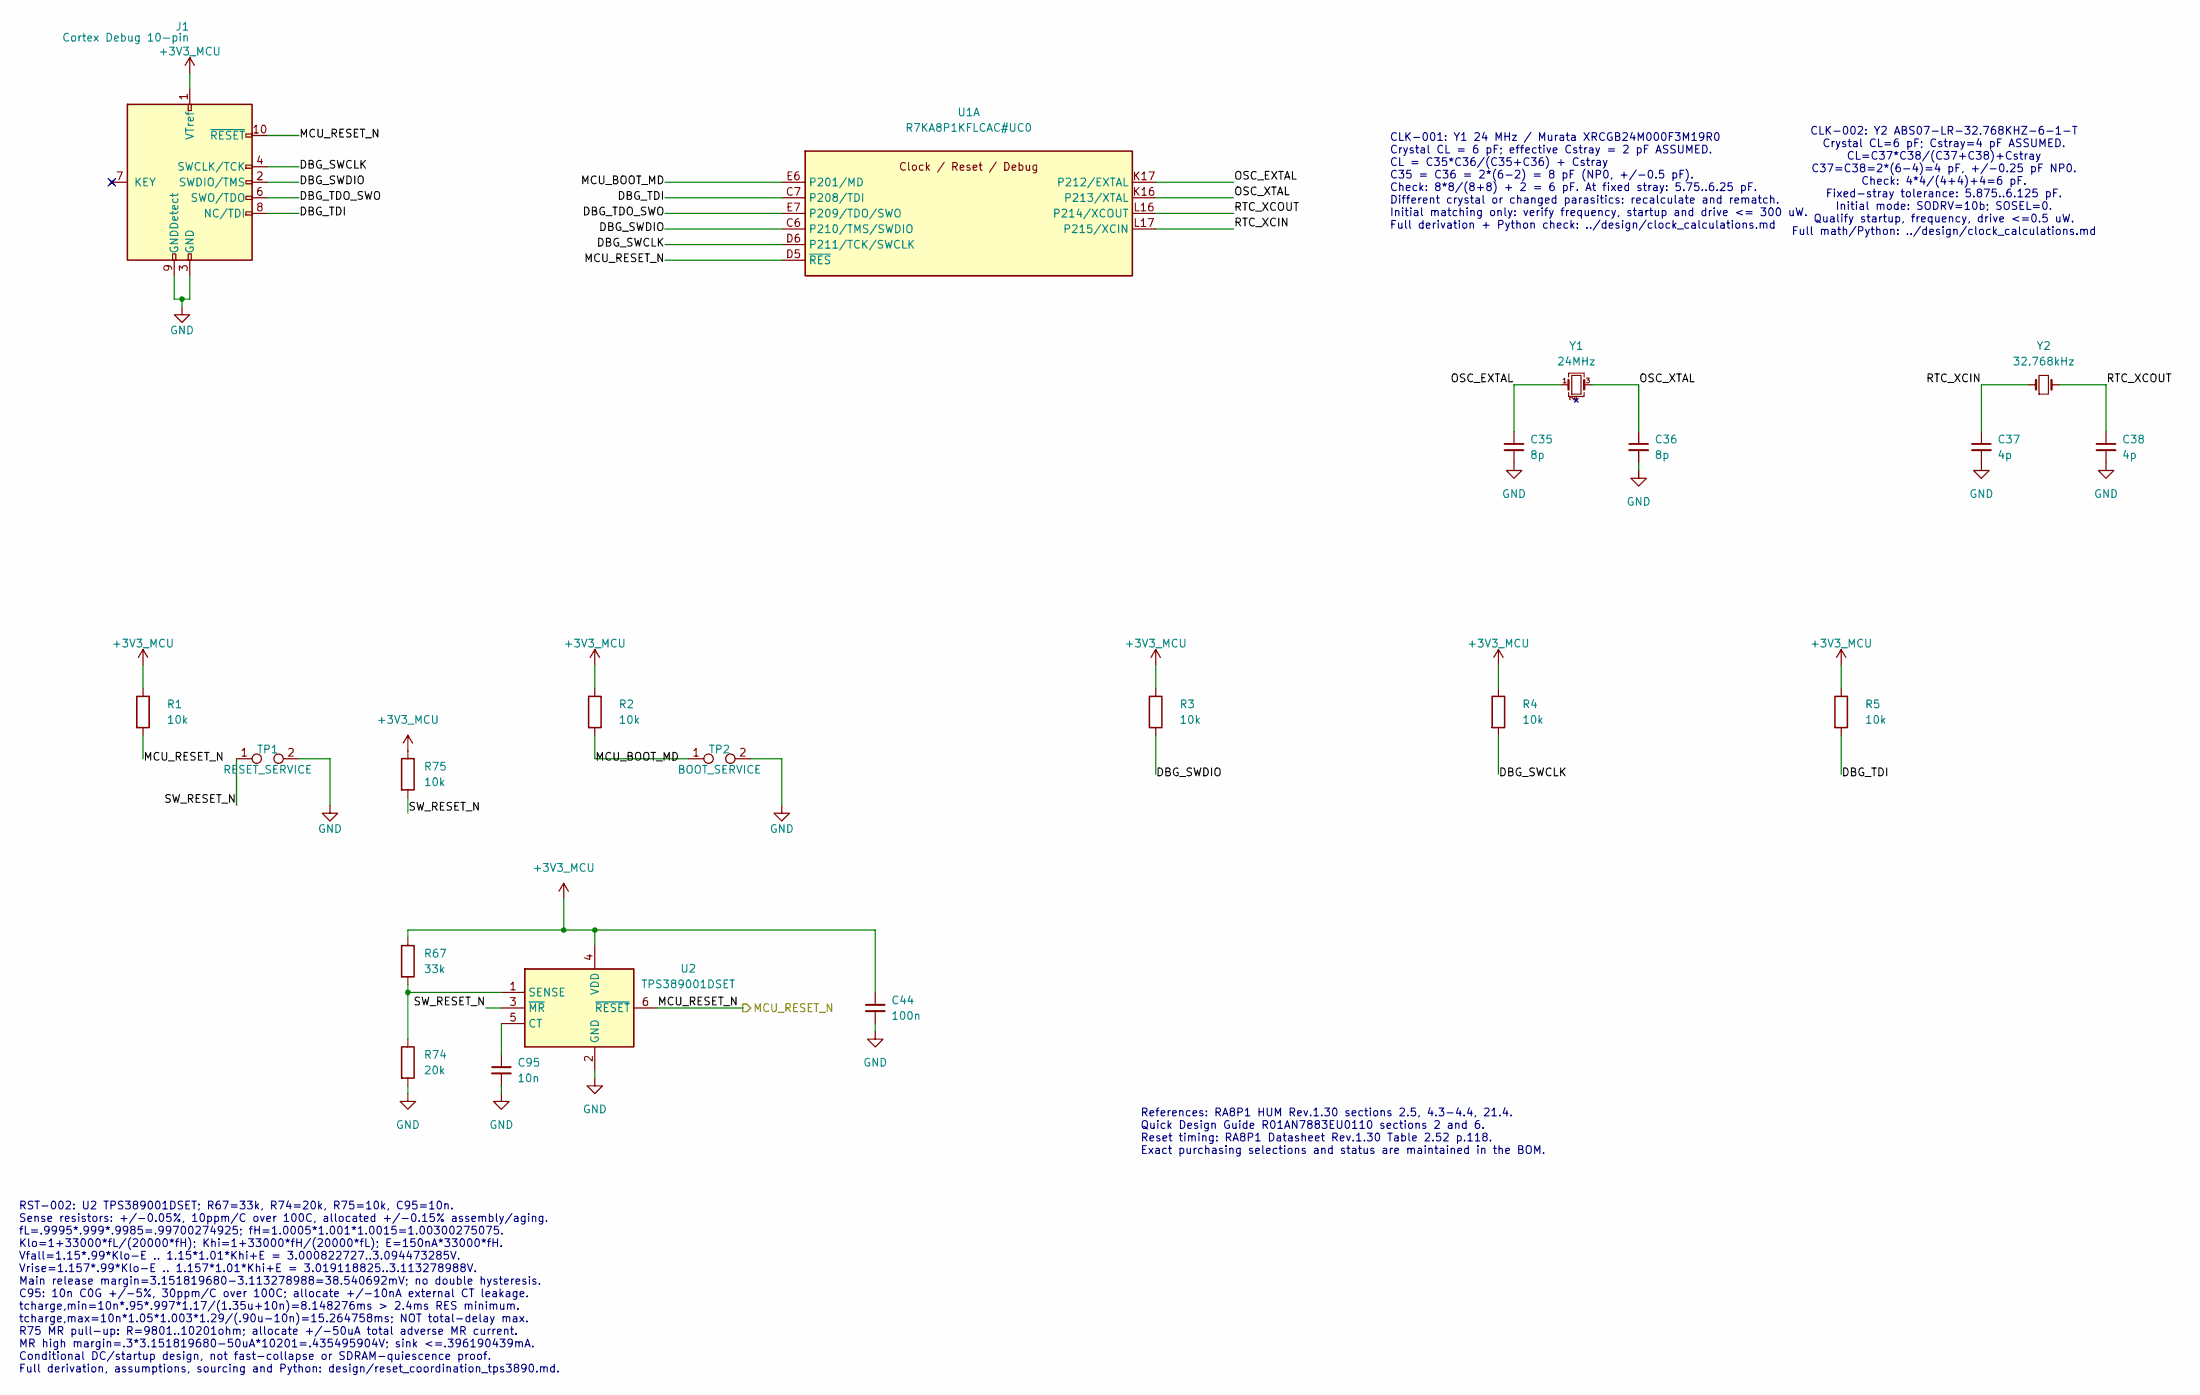
[picture p35: schematic mcu_clocks_debug.kicad_sch]

Parts:
C35, C36: 8p; Manufacturer_Part_Number C1005NP01H080D050BA; DigiKey_Part_Number 445-13781-1-ND
C37, C38: 4p; Manufacturer_Part_Number C1005NP01H040C050BA; DigiKey_Part_Number 445-13777-1-ND
C44: 100n; Manufacturer_Part_Number C1608X7R1H104K080AA; DigiKey_Part_Number 445-1314-1-ND
C95: 10n; Manufacturer_Part_Number GRM1885C1H103JA01D; DigiKey_Part_Number 490-9666-1-ND
J1: Cortex Debug 10-pin
R1, R2, R3, R4, R5, R75: 10k; Manufacturer_Part_Number RC0603FR-0710KL; DigiKey_Part_Number 311-10.0KHRCT-ND
R67: 33k; Manufacturer_Part_Number ERA-6ARW333V; DigiKey_Part_Number P33KBSCT-ND
R74: 20k; Manufacturer_Part_Number RG1608N-203-W-T1; DigiKey_Part_Number RG16N20.0KWCT-ND
TP1: RESET_SERVICE
TP2: BOOT_SERVICE
U1: R7KA8P1KFLCAC#UC0; BGA289C65P17X17_1200X1200X138; Mouser Part Number 968-R7KA8P1KFLCACUC0
U2: TPS389001DSET; Manufacturer_Part_Number TPS389001DSET; DigiKey_Part_Number 296-44489-1-ND
Y1: 24MHz; Manufacturer_Part_Number XRCGB24M000F3M19R0; DigiKey_Part_Number 490-18296-1-ND
Y2: 32.768kHz; Manufacturer_Part_Number ABS07-LR-32.768KHZ-6-1-T; DigiKey_Part_Number 535-12943-1-ND

Connections:
+3V3_MCU: C44.1, J1.1 (VTref), R1.1, R2.1, R3.1, R4.1, R5.1, R67.1, R75.1, U2.4 (VDD)
DBG_SWCLK: J1.4 (SWCLK/TCK), R4.2, U1.D6 (P211/TCK/SWCLK)
DBG_SWDIO: J1.2 (SWDIO/TMS), R3.2, U1.C6 (P210/TMS/SWDIO)
DBG_TDI: J1.8 (NC/TDI), R5.2, U1.C7 (P208/TDI)
DBG_TDO_SWO: J1.6 (SWO/TDO), U1.E7 (P209/TDO/SWO)
GND: C35.2, C36.2, C37.2, C38.2, C44.2, C95.2, J1.3 (GND), J1.5 (GND), J1.9 (GNDDetect), R74.2, TP1.2, TP2.2, U2.2 (GND)
MCU_BOOT_MD: R2.2, TP2.1, U1.E6 (P201/MD)
MCU_RESET_N: J1.10 (~RESET), R1.2, U1.D5 (~RES), U2.6 (~RESET)
unnamed: C95.1, U2.5 (CT)
unnamed: R67.2, R74.1, U2.1 (SENSE)
unnamed: Y1.2 (NC), Y1.4 (NC)
OSC_EXTAL: C35.1, U1.K17 (P212/EXTAL), Y1.1
OSC_XTAL: C36.1, U1.K16 (P213/XTAL), Y1.3
RTC_XCIN: C37.1, U1.L17 (P215/XCIN), Y2.1
RTC_XCOUT: C38.1, U1.L16 (P214/XCOUT), Y2.2
SW_RESET_N: R75.2, TP1.1, U2.3 (~MR)

Notes on the sheet:
CLK-001: Y1 24 MHz / Murata XRCGB24M000F3M19R0 Crystal CL = 6 pF; effective Cstray = 2 pF ASSUMED. CL = C35*C36/(C35+C36) + Cstray C35 = C36 = 2*(6-2) = 8 pF (NP0, +/-0.5 pF). Check: 8*8/(8+8) + 2 = 6 pF. At fixed stray: 5.75..6.25 pF. Different crystal or changed parasitics: recalculate and rematc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
RST-002: U2 TPS389001DSET; R67=33k, R74=20k, R75=10k, C95=10n. Sense resistors: +/-0.05%, 10ppm/C over 100C, allocated +/-0.15% assembly/aging. fL=.9995*.999*.9985=.99700274925; fH=1.0005*1.001*1.0015=1.00300275075. Klo=1+33000*fL/(20000*fH); Khi=1+33000*fH/(20000*fL); E=150nA*33000*fH. Vfall=1.15*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
References: RA8P1 HUM Rev.1.30 sections 2.5, 4.3-4.4, 21.4. Quick Design Guide R01AN7883EU0110 sections 2 and 6. Reset timing: RA8P1 Datasheet Rev.1.30 Table 2.52 p.118. Exact purchasing selections and status are maintained in the BOM.
CLK-002: Y2 ABS07-LR-32.768KHZ-6-1-T Crystal CL=6 pF; Cstray=4 pF ASSUMED. CL=C37*C38/(C37+C38)+Cstray C37=C38=2*(6-4)=4 pF, +/-0.25 pF NP0. Check: 4*4/(4+4)+4=6 pF. Fixed-stray tolerance: 5.875..6.125 pF. Initial mode: SODRV=10b; SOSEL=0. Qualify startup, frequency, drive <=0.5 uW. Full math/Pytho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
