bsikar/ra8p1-ereader-kicad/ereader/mcu_interfaces.kicad_sch

## KiCad design ereader/mcu_interfaces.kicad_sch (2026-10-07)

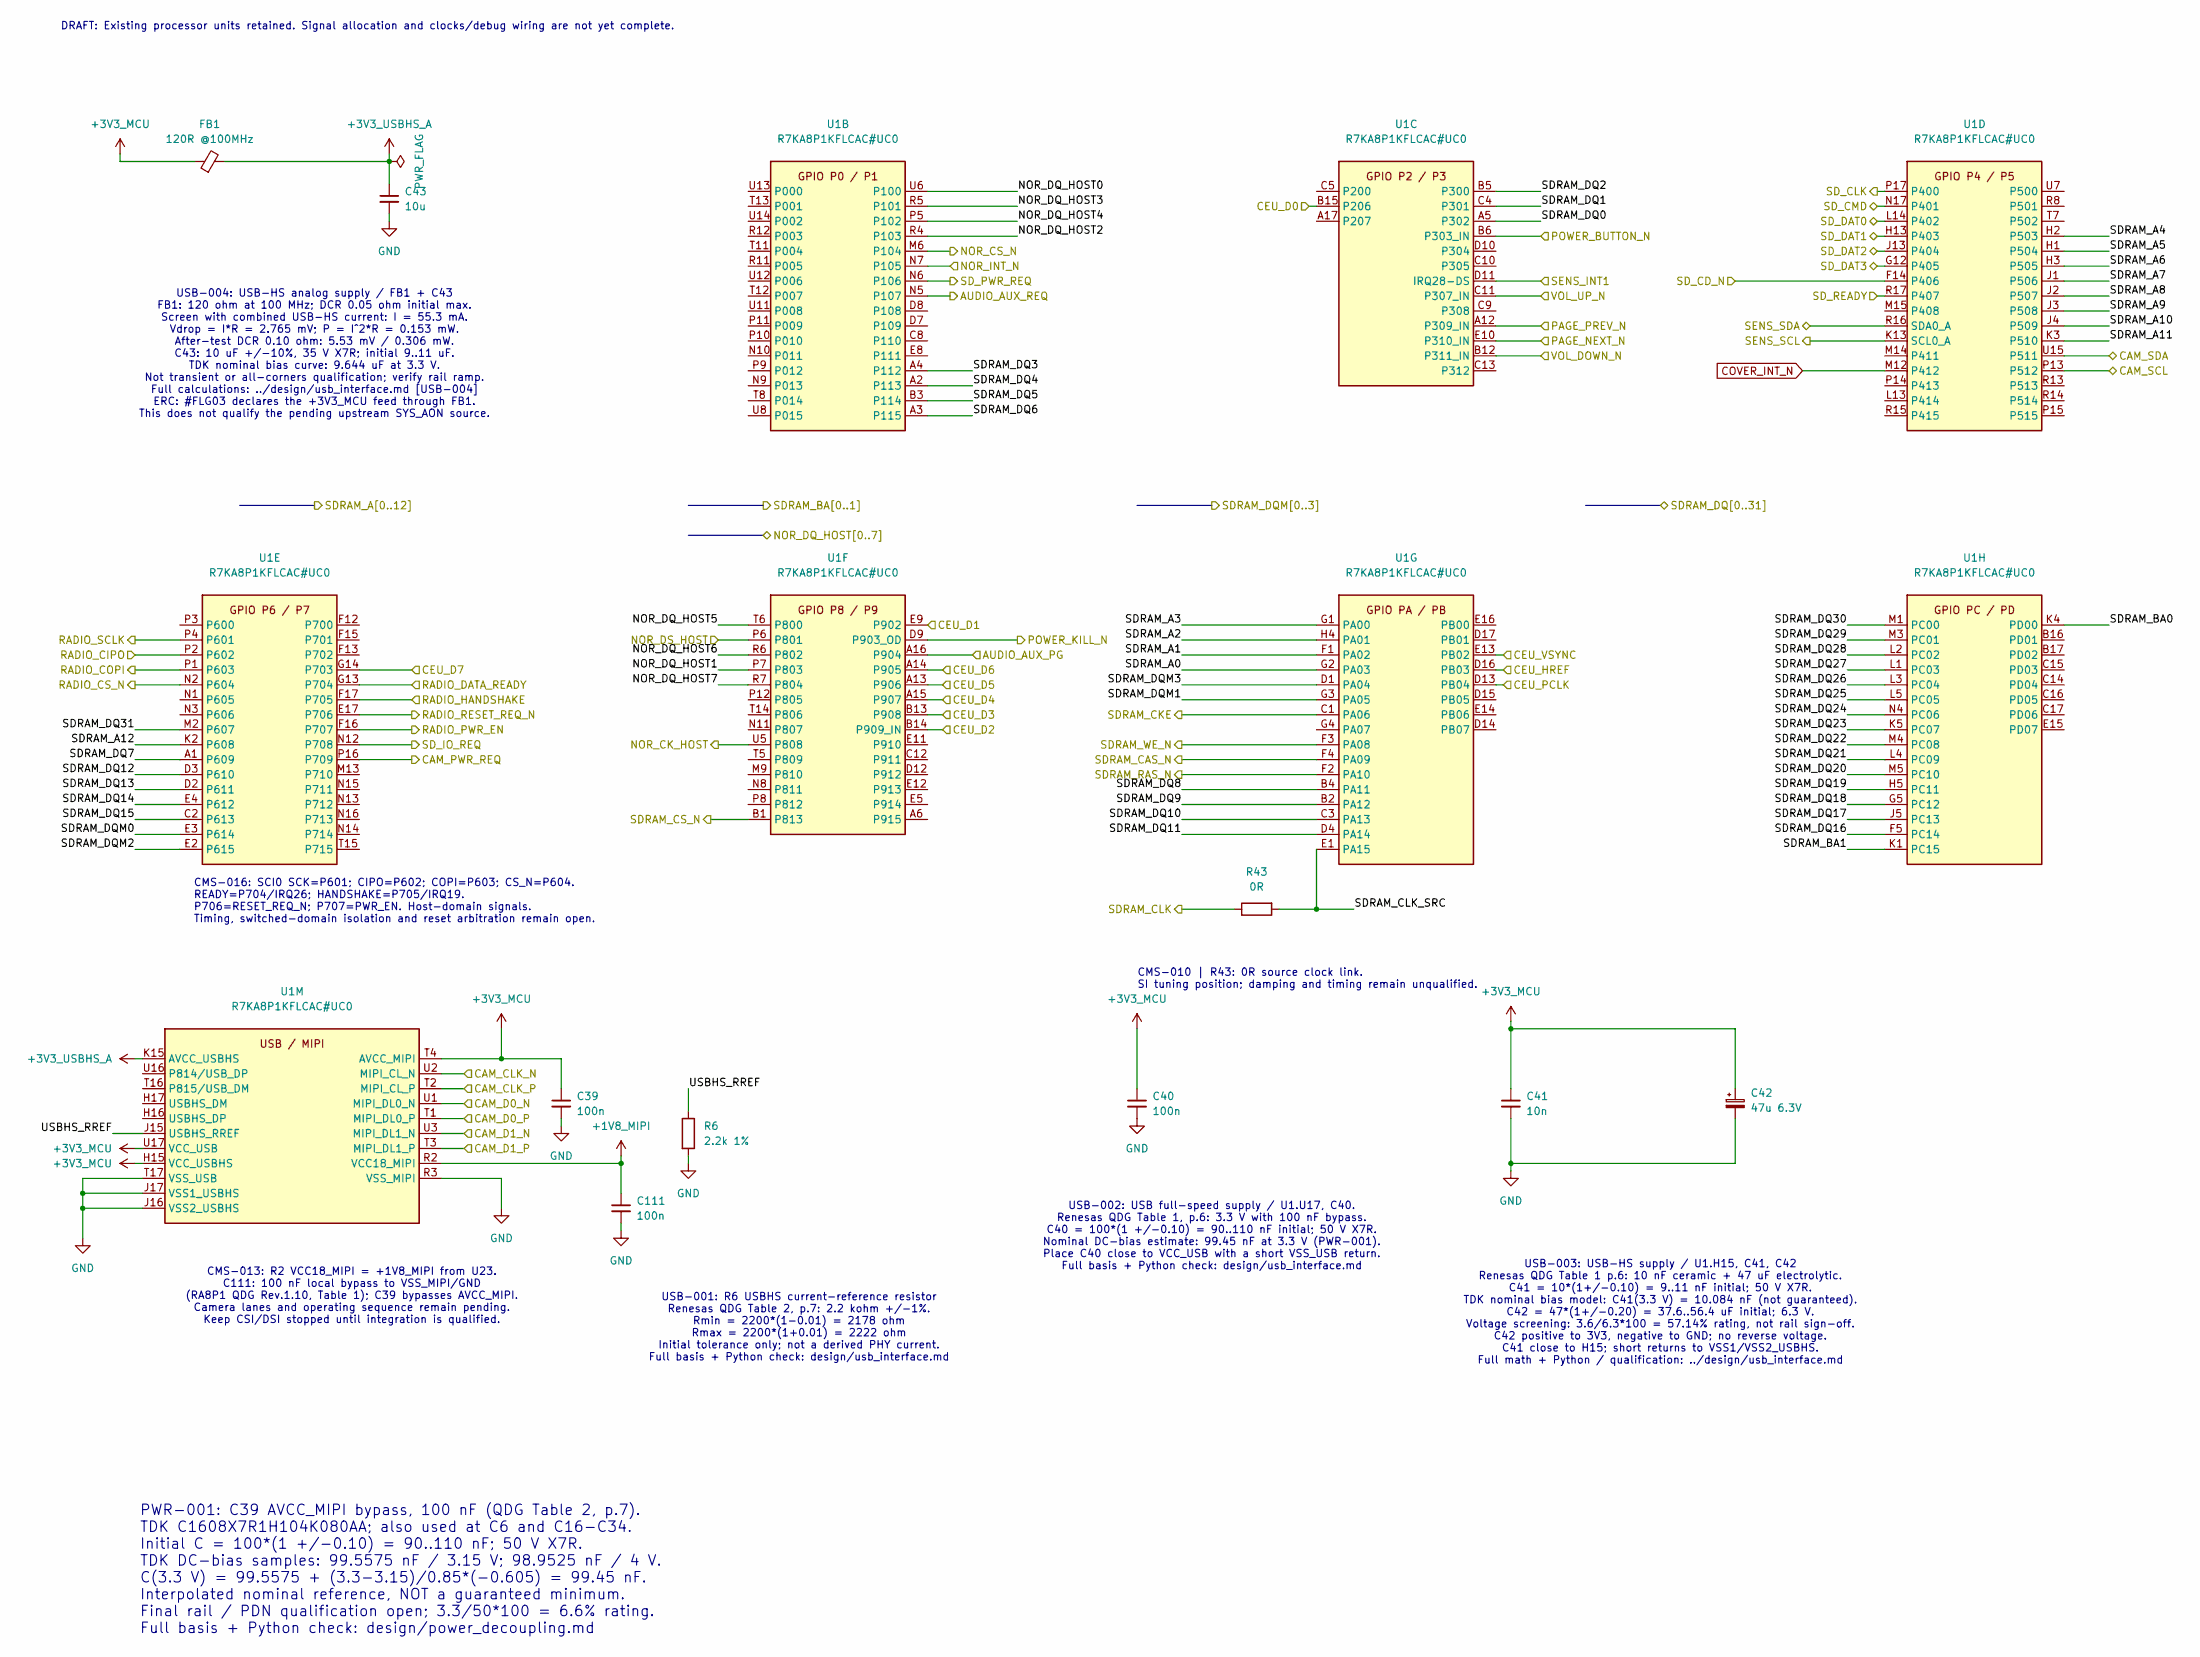
[picture p37: schematic mcu_interfaces.kicad_sch]

Parts:
C39, C40, C111: 100n; Manufacturer_Part_Number C1608X7R1H104K080AA; DigiKey_Part_Number 445-1314-1-ND
C41: 10n; Manufacturer_Part_Number C1608X7R1H103K080AA; DigiKey_Part_Number 445-1311-1-ND
C42: 47u 6.3V; Manufacturer_Part_Number EEE-FP0J470AR; DigiKey_Part_Number PCE4511CT-ND
C43: 10u; Manufacturer_Part_Number C3216X7R1V106K160AC; DigiKey_Part_Number 445-14799-1-ND
FB1: 120R @100MHz; Manufacturer_Part_Number BLM18PG121SN1D; DigiKey_Part_Number 490-1037-1-ND
R6: 2.2k 1%; Manufacturer_Part_Number RC0603FR-072K2L; DigiKey_Part_Number 311-2.20KHRCT-ND
R43: 0R; Manufacturer_Part_Number RC0603JR-070RL; DigiKey_Part_Number 311-0.0GRCT-ND
U1: R7KA8P1KFLCAC#UC0; BGA289C65P17X17_1200X1200X138; Mouser Part Number 968-R7KA8P1KFLCACUC0

Connections:
+1V8_MIPI: C111.1, U1.R2 (VCC18_MIPI)
+3V3_MCU: C39.1, C40.1, C41.1, C42.1, FB1.1, U1.H15 (VCC_USBHS), U1.T4 (AVCC_MIPI), U1.U17 (VCC_USB)
+3V3_USBHS_A: C43.1, FB1.2, U1.K15 (AVCC_USBHS)
AUDIO_AUX_PG: U1.A16 (P904)
AUDIO_AUX_REQ: U1.N5 (P107)
CAM_CLK_N: U1.U2 (MIPI_CL_N)
CAM_CLK_P: U1.T2 (MIPI_CL_P)
CAM_D0_N: U1.U1 (MIPI_DL0_N)
CAM_D0_P: U1.T1 (MIPI_DL0_P)
CAM_D1_N: U1.U3 (MIPI_DL1_N)
CAM_D1_P: U1.T3 (MIPI_DL1_P)
CAM_PWR_REQ: U1.P16 (P709)
CAM_SCL: U1.P13 (P512)
CAM_SDA: U1.U15 (P511)
CEU_D0: U1.B15 (P206)
CEU_D1: U1.E9 (P902)
CEU_D2: U1.B14 (P909)
CEU_D3: U1.B13 (P908)
CEU_D4: U1.A15 (P907)
CEU_D5: U1.A13 (P906)
CEU_D6: U1.A14 (P905)
CEU_D7: U1.G14 (P703)
CEU_HREF: U1.D16 (PB03)
CEU_PCLK: U1.D13 (PB04)
CEU_VSYNC: U1.E13 (PB02)
COVER_INT_N: U1.M12 (P412)
GND: C39.2, C40.2, C41.2, C42.2, C43.2, C111.2, R6.2, U1.J16 (VSS2_USBHS), U1.J17 (VSS1_USBHS), U1.R3 (VSS_MIPI), U1.T17 (VSS_USB)
NOR_CK_HOST: U1.U5 (P808)
NOR_CS_N: U1.M6 (P104)
NOR_DQ_HOST0: U1.U6 (P100)
NOR_DQ_HOST1: U1.P7 (P803)
NOR_DQ_HOST2: U1.R4 (P103)
NOR_DQ_HOST3: U1.R5 (P101)
NOR_DQ_HOST4: U1.P5 (P102)
NOR_DQ_HOST5: U1.T6 (P800)
NOR_DQ_HOST6: U1.R6 (P802)
NOR_DQ_HOST7: U1.R7 (P804)
NOR_DS_HOST: U1.P6 (P801)
NOR_INT_N: U1.N7 (P105)
PAGE_NEXT_N: U1.E10 (P310)
PAGE_PREV_N: U1.A12 (P309)
POWER_BUTTON_N: U1.B6 (P303)
POWER_KILL_N: U1.D9 (P903)
RADIO_CIPO: U1.P2 (P602)
RADIO_COPI: U1.P1 (P603)
RADIO_CS_N: U1.N2 (P604)
RADIO_DATA_READY: U1.G13 (P704)
RADIO_HANDSHAKE: U1.F17 (P705)
RADIO_PWR_EN: U1.F16 (P707)
RADIO_RESET_REQ_N: U1.E17 (P706)
RADIO_SCLK: U1.P4 (P601)
SDRAM_A0: U1.G2 (PA03)
SDRAM_A1: U1.F1 (PA02)
SDRAM_A2: U1.H4 (PA01)
SDRAM_A3: U1.G1 (PA00)
SDRAM_A4: U1.H2 (P503)
SDRAM_A5: U1.H1 (P504)
SDRAM_A6: U1.H3 (P505)
SDRAM_A7: U1.J1 (P506)
SDRAM_A8: U1.J2 (P507)
SDRAM_A9: U1.J3 (P508)
SDRAM_A10: U1.J4 (P509)
SDRAM_A11: U1.K3 (P510)
SDRAM_A12: U1.K2 (P608)
SDRAM_BA0: U1.K4 (PD00)
SDRAM_BA1: U1.K1 (PC15)
SDRAM_CAS_N: U1.F4 (PA09)
SDRAM_CKE: U1.C1 (PA06)
SDRAM_CLK: R43.1
SDRAM_CLK_SRC: R43.2, U1.E1 (PA15)
SDRAM_CS_N: U1.B1 (P813)
SDRAM_DQ0: U1.A5 (P302)
SDRAM_DQ1: U1.C4 (P301)
SDRAM_DQ2: U1.B5 (P300)
SDRAM_DQ3: U1.A4 (P112)
SDRAM_DQ4: U1.A2 (P113)
SDRAM_DQ5: U1.B3 (P114)
SDRAM_DQ6: U1.A3 (P115)
SDRAM_DQ7: U1.A1 (P609)
SDRAM_DQ8: U1.B4 (PA11)
SDRAM_DQ9: U1.B2 (PA12)
SDRAM_DQ10: U1.C3 (PA13)
SDRAM_DQ11: U1.D4 (PA14)
SDRAM_DQ12: U1.D3 (P610)
SDRAM_DQ13: U1.D2 (P611)
SDRAM_DQ14: U1.E4 (P612)
SDRAM_DQ15: U1.C2 (P613)
SDRAM_DQ16: U1.F5 (PC14)
SDRAM_DQ17: U1.J5 (PC13)
SDRAM_DQ18: U1.G5 (PC12)
SDRAM_DQ19: U1.H5 (PC11)
SDRAM_DQ20: U1.M5 (PC10)
SDRAM_DQ21: U1.L4 (PC09)
SDRAM_DQ22: U1.M4 (PC08)
SDRAM_DQ23: U1.K5 (PC07)
SDRAM_DQ24: U1.N4 (PC06)
SDRAM_DQ25: U1.L5 (PC05)
SDRAM_DQ26: U1.L3 (PC04)
SDRAM_DQ27: U1.L1 (PC03)
SDRAM_DQ28: U1.L2 (PC02)
SDRAM_DQ29: U1.M3 (PC01)
SDRAM_DQ30: U1.M1 (PC00)
SDRAM_DQ31: U1.M2 (P607)
SDRAM_DQM0: U1.E3 (P614)
SDRAM_DQM1: U1.G3 (PA05)
SDRAM_DQM2: U1.E2 (P615)
SDRAM_DQM3: U1.D1 (PA04)
SDRAM_RAS_N: U1.F2 (PA10)
SDRAM_WE_N: U1.F3 (PA08)
SD_CD_N: U1.F14 (P406)
SD_CLK: U1.P17 (P400)
SD_CMD: U1.N17 (P401)
SD_DAT0: U1.L14 (P402)
SD_DAT1: U1.H13 (P403)
SD_DAT2: U1.J13 (P404)
SD_DAT3: U1.G12 (P405)
SD_IO_REQ: U1.N12 (P708)
SD_PWR_REQ: U1.N6 (P106)
SD_READY: U1.R17 (P407)
SENS_INT1: U1.D11 (P306)
SENS_SCL: U1.K13 (P410)
SENS_SDA: U1.R16 (P409)
USBHS_RREF: R6.1, U1.J15 (USBHS_RREF)
VOL_DOWN_N: U1.B12 (P311)
VOL_UP_N: U1.C11 (P307)

Notes on the sheet:
DRAFT: Existing processor units retained. Signal allocation and clocks/debug wiring are not yet complete.
USB-001: R6 USBHS current-reference resistor Renesas QDG Table 2, p.7: 2.2 kohm +/-1%. Rmin = 2200*(1-0.01) = 2178 ohm Rmax = 2200*(1+0.01) = 2222 ohm Initial tolerance only; not a derived PHY current. Full basis + Python check: design/usb_interface.md
CMS-010 | R43: 0R source clock link. SI tuning position; damping and timing remain unqualified.
USB-004: USB-HS analog supply / FB1 + C43 FB1: 120 ohm at 100 MHz; DCR 0.05 ohm initial max. Screen with combined USB-HS current: I = 55.3 mA. Vdrop = I*R = 2.765 mV; P = I^2*R = 0.153 mW. After-test DCR 0.10 ohm: 5.53 mV / 0.306 mW. C43: 10 uF +/-10%, 35 V X7R; initial 9..11 uF. TDK nominal bias c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
CMS-016: SCI0 SCK=P601; CIPO=P602; COPI=P603; CS_N=P604. READY=P704/IRQ26; HANDSHAKE=P705/IRQ19. P706=RESET_REQ_N; P707=PWR_EN. Host-domain signals. Timing, switched-domain isolation and reset arbitration remain open.
USB-002: USB full-speed supply / U1.U17, C40. Renesas QDG Table 1, p.6: 3.3 V with 100 nF bypass. C40 = 100*(1 +/-0.10) = 90..110 nF initial; 50 V X7R. Nominal DC-bias estimate: 99.45 nF at 3.3 V (PWR-001). Place C40 close to VCC_USB with a short VSS_USB return. Full basis + Python check: design/us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
PWR-001: C39 AVCC_MIPI bypass, 100 nF (QDG Table 2, p.7). TDK C1608X7R1H104K080AA; also used at C6 and C16-C34. Initial C = 100*(1 +/-0.10) = 90..110 nF; 50 V X7R. TDK DC-bias samples: 99.5575 nF / 3.15 V; 98.9525 nF / 4 V. C(3.3 V) = 99.5575 + (3.3-3.15)/0.85*(-0.605) = 99.45 nF. Interpolated nomi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
CMS-013: R2 VCC18_MIPI = +1V8_MIPI from U23. C111: 100 nF local bypass to VSS_MIPI/GND (RA8P1 QDG Rev.1.10, Table 1); C39 bypasses AVCC_MIPI. Camera lanes and operating sequence remain pending. Keep CSI/DSI stopped until integration is qualified.
USB-003: USB-HS supply / U1.H15, C41, C42 Renesas QDG Table 1 p.6: 10 nF ceramic + 47 uF electrolytic. C41 = 10*(1+/-0.10) = 9..11 nF initial; 50 V X7R. TDK nominal bias model: C41(3.3 V) = 10.084 nF (not guaranteed). C42 = 47*(1+/-0.20) = 37.6..56.4 uF initial; 6.3 V. Voltage screening: 3.6/6.3*10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
