bsikar/ra8p1-ereader-kicad/ereader/mcu_supply_power.kicad_sch

## KiCad design ereader/mcu_supply_power.kicad_sch (2026-10-07)

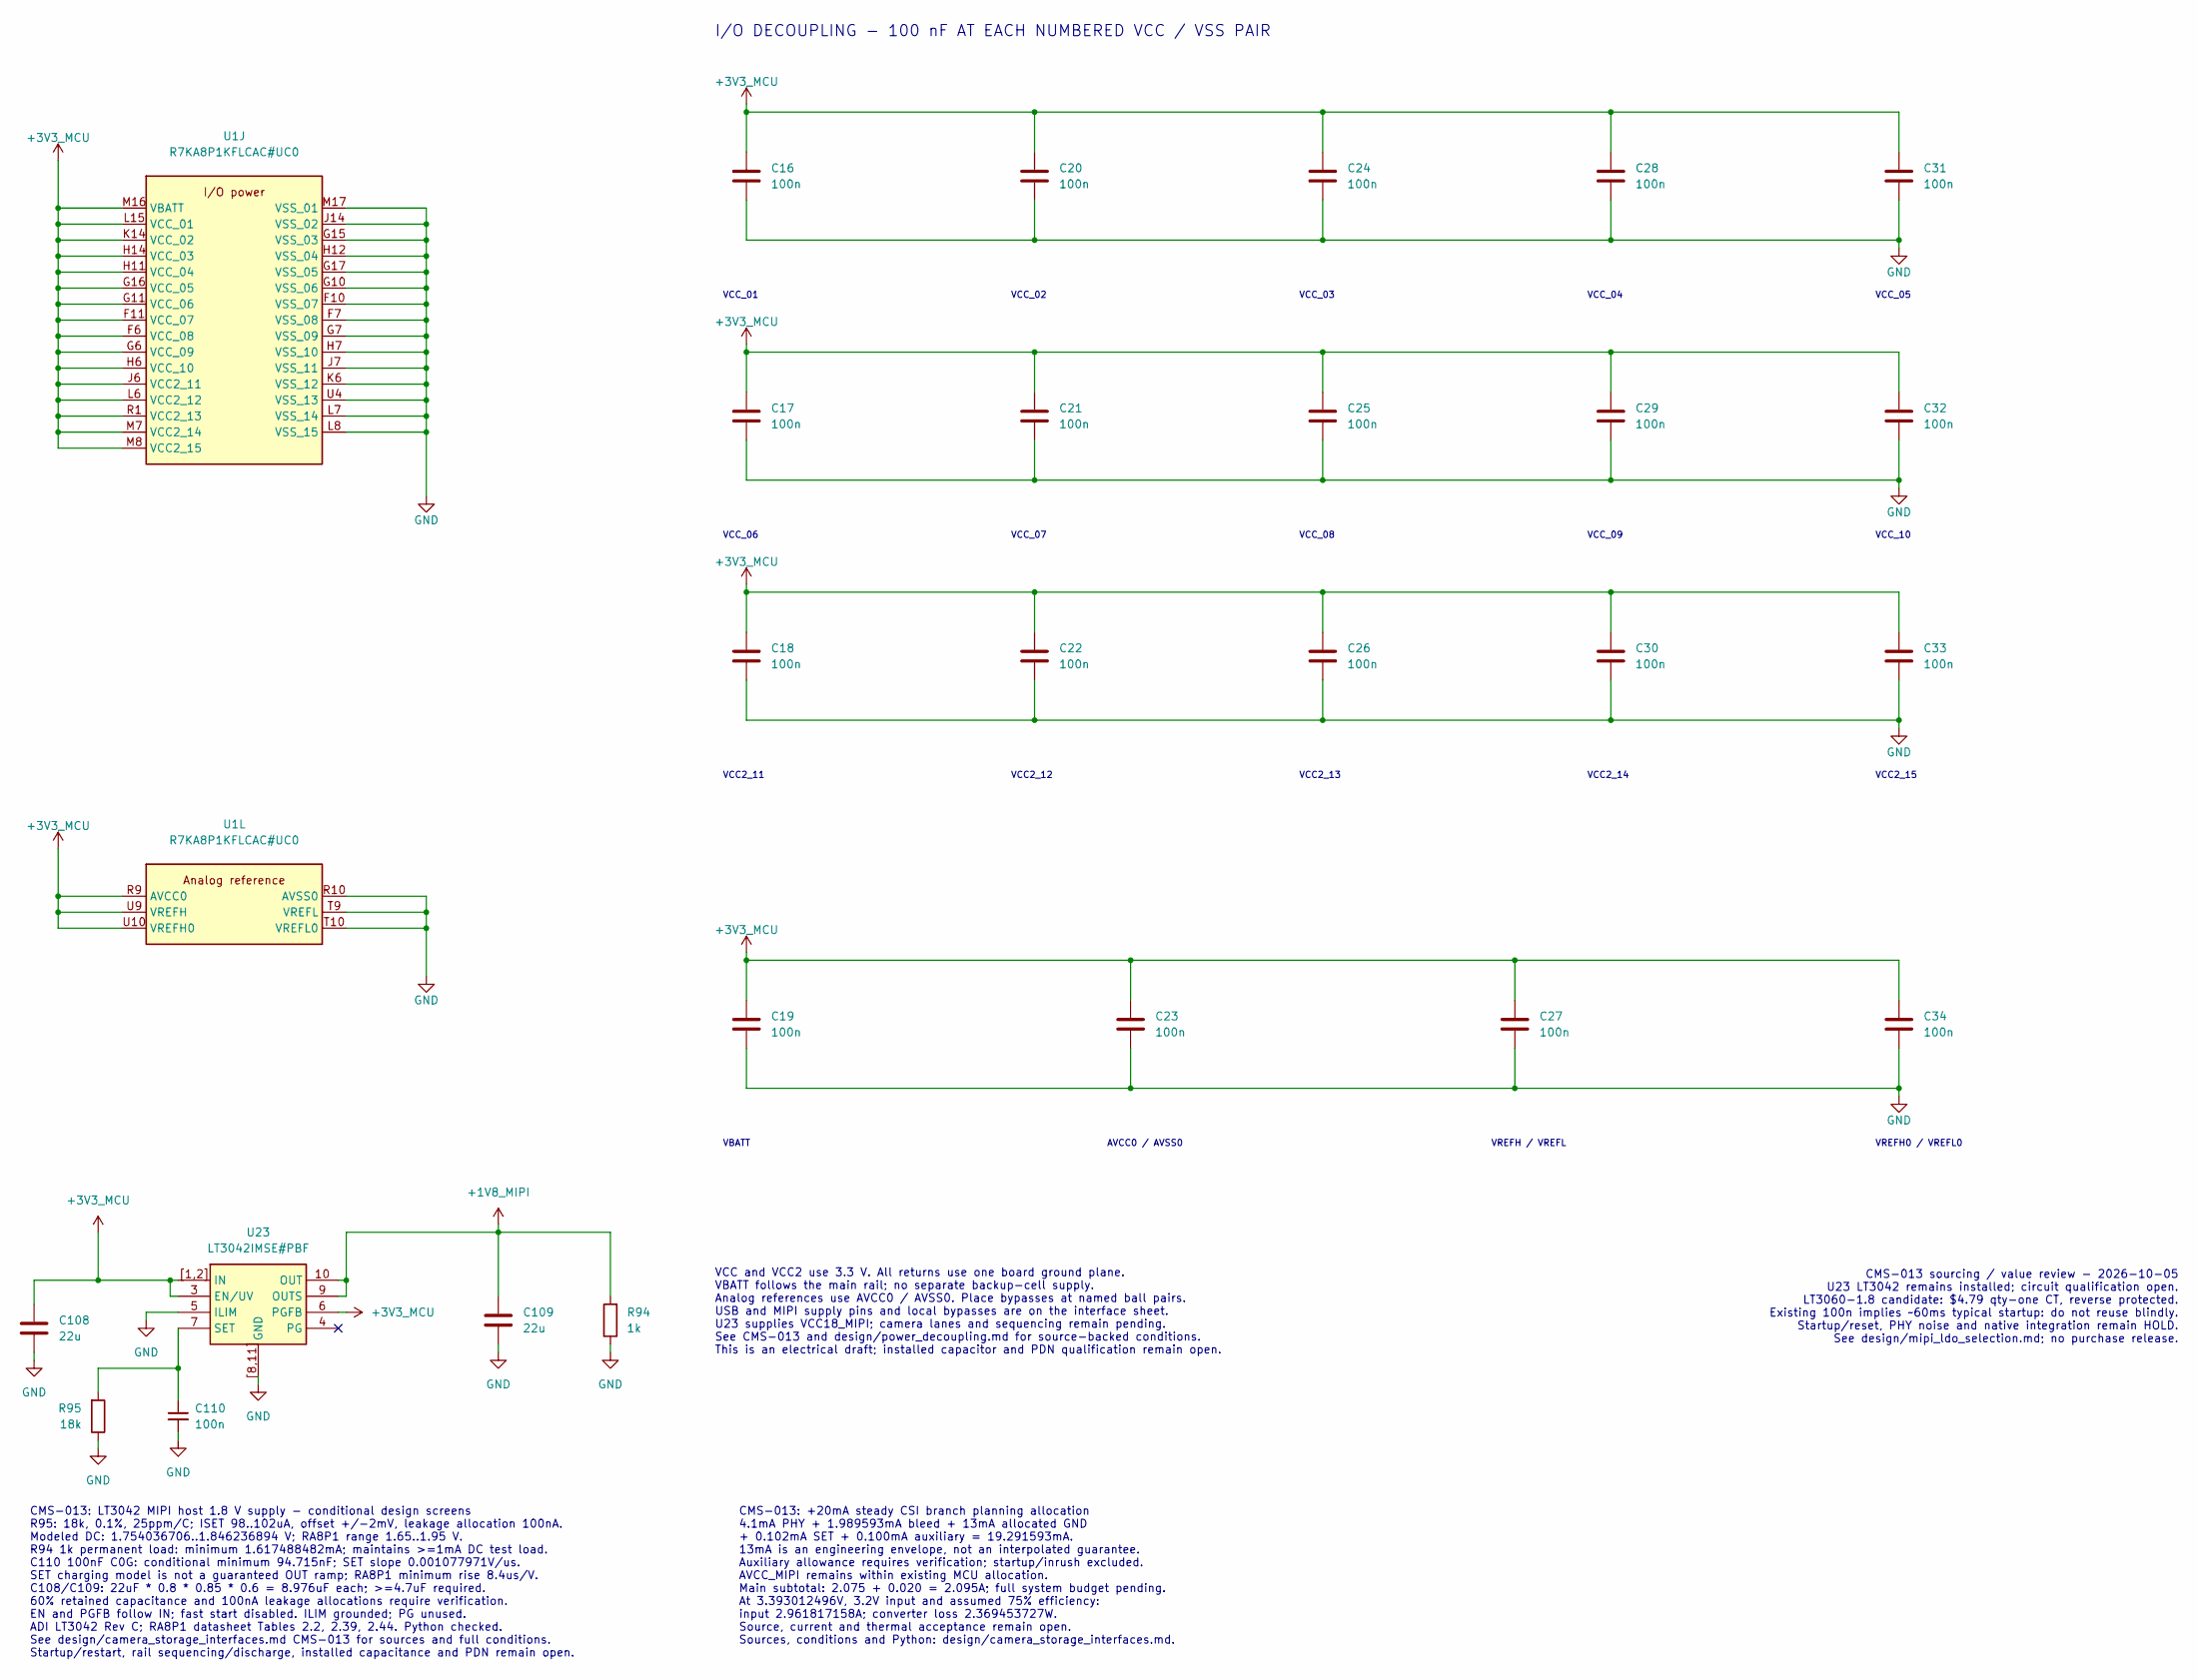
[picture p38: schematic mcu_supply_power.kicad_sch]

Parts:
C16, C17, C18, C19, C20, C21, C22, C23, C24, C25, C26, C27, C28, C29, C30, C31, C32, C33, C34: 100n; Manufacturer_Part_Number C1608X7R1H104K080AA; DigiKey_Part_Number 445-1314-1-ND
C108, C109: 22u; Manufacturer_Part_Number CL32B226MOJNNNE; DigiKey_Part_Number 1276-3395-1-ND
C110: 100n; Manufacturer_Part_Number GRM31C5C1H104JA01K; DigiKey_Part_Number 490-8335-1-ND
R94: 1k; Manufacturer_Part_Number RC0603FR-071KL; DigiKey_Part_Number 311-1.00KHRCT-ND
R95: 18k; Manufacturer_Part_Number RT0603BRD0718KL; DigiKey_Part_Number YAG1552CT-ND
U1: R7KA8P1KFLCAC#UC0; BGA289C65P17X17_1200X1200X138; Mouser Part Number 968-R7KA8P1KFLCACUC0
U23: LT3042IMSE#PBF; MSOP-10-1EP_3x3mm_P0.5mm_EP1.68x1.88mm; Manufacturer_Part_Number LT3042IMSE#PBF; Mouser Part Number 584-LT3042IMSE#PBF

Connections:
+1V8_MIPI: C109.1, R94.2, U23.9 (OUTS), U23.10 (OUT)
+3V3_MCU: C16.1, C17.1, C18.1, C19.1, C20.1, C21.1, C22.1, C23.1, C24.1, C25.1, C26.1, C27.1, C28.1, C29.1, C30.1, C31.1, C32.1, C33.1, C34.1, C108.1, U1.F6 (VCC_08), U1.F11 (VCC_07), U1.G6 (VCC_09), U1.G11 (VCC_06), U1.G16 (VCC_05), U1.H6 (VCC_10), U1.H11 (VCC_04), U1.H14 (VCC_03), U1.J6 (VCC2_11), U1.K14 (VCC_02), U1.L6 (VCC2_12), U1.L15 (VCC_01), U1.M7 (VCC2_14), U1.M8 (VCC2_15), U1.M16 (VBATT), U1.R1 (VCC2_13), U1.R9 (AVCC0), U1.U9 (VREFH), U1.U10 (VREFH0), U23.3 (EN/UV), U23.6 (PGFB), U23.[1,2] (IN)
GND: C16.2, C17.2, C18.2, C19.2, C20.2, C21.2, C22.2, C23.2, C24.2, C25.2, C26.2, C27.2, C28.2, C29.2, C30.2, C31.2, C32.2, C33.2, C34.2, C108.2, C109.2, C110.2, R94.1, R95.1, U1.F7 (VSS_08), U1.F10 (VSS_07), U1.G7 (VSS_09), U1.G10 (VSS_06), U1.G15 (VSS_03), U1.G17 (VSS_05), U1.H7 (VSS_10), U1.H12 (VSS_04), U1.J7 (VSS_11), U1.J14 (VSS_02), U1.K6 (VSS_12), U1.L7 (VSS_14), U1.L8 (VSS_15), U1.M17 (VSS_01), U1.R10 (AVSS0), U1.T9 (VREFL), U1.T10 (VREFL0), U1.U4 (VSS_13), U23.5 (ILIM), U23.[8,11] (GND)
unnamed: C110.1, R95.2, U23.7 (SET)

Notes on the sheet:
VREFH0 / VREFL0
VCC_02
VCC2_15
VBATT
VCC_06
CMS-013: LT3042 MIPI host 1.8 V supply - conditional design screens R95: 18k, 0.1%, 25ppm/C; ISET 98..102uA, offset +/-2mV, leakage allocation 100nA. Modeled DC: 1.754036706..1.846236894 V; RA8P1 range 1.65..1.95 V. R94 1k permanent load: minimum 1.617488482mA; maintains >=1mA DC test load. C110 10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
VREFH / VREFL
VCC_09
VCC_01
VCC_05
VCC2_13
VCC_08
AVCC0 / AVSS0
VCC2_11
VCC_03
CMS-013 sourcing / value review - 2026-10-05 U23 LT3042 remains installed; circuit qualification open. LT3060-1.8 candidate: $4.79 qty-one CT, reverse protected. Existing 100n implies ~60ms typical startup: do not reuse blindly. Startup/reset, PHY noise and native integration remain HOLD. See desig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
I/O DECOUPLING - 100 nF AT EACH NUMBERED VCC / VSS PAIR
VCC_04
VCC_07
CMS-013: +20mA steady CSI branch planning allocation 4.1mA PHY + 1.989593mA bleed + 13mA allocated GND + 0.102mA SET + 0.100mA auxiliary = 19.291593mA. 13mA is an engineering envelope, not an interpolated guarantee. Auxiliary allowance requires verification; startup/inrush excluded. AVCC_MIPI remai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
VCC_10
VCC2_14
VCC2_12
VCC and VCC2 use 3.3 V. All returns use one board ground plane. VBATT follows the main rail; no separate backup-cell supply. Analog references use AVCC0 / AVSS0. Place bypasses at named ball pairs. USB and MIPI supply pins and local bypasses are on the interface sheet. U23 supplies VCC18_MIPI; came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
