bsikar/ra8p1-ereader-kicad/ereader/nor_flash.kicad_sch

## KiCad design ereader/nor_flash.kicad_sch (2026-10-07)

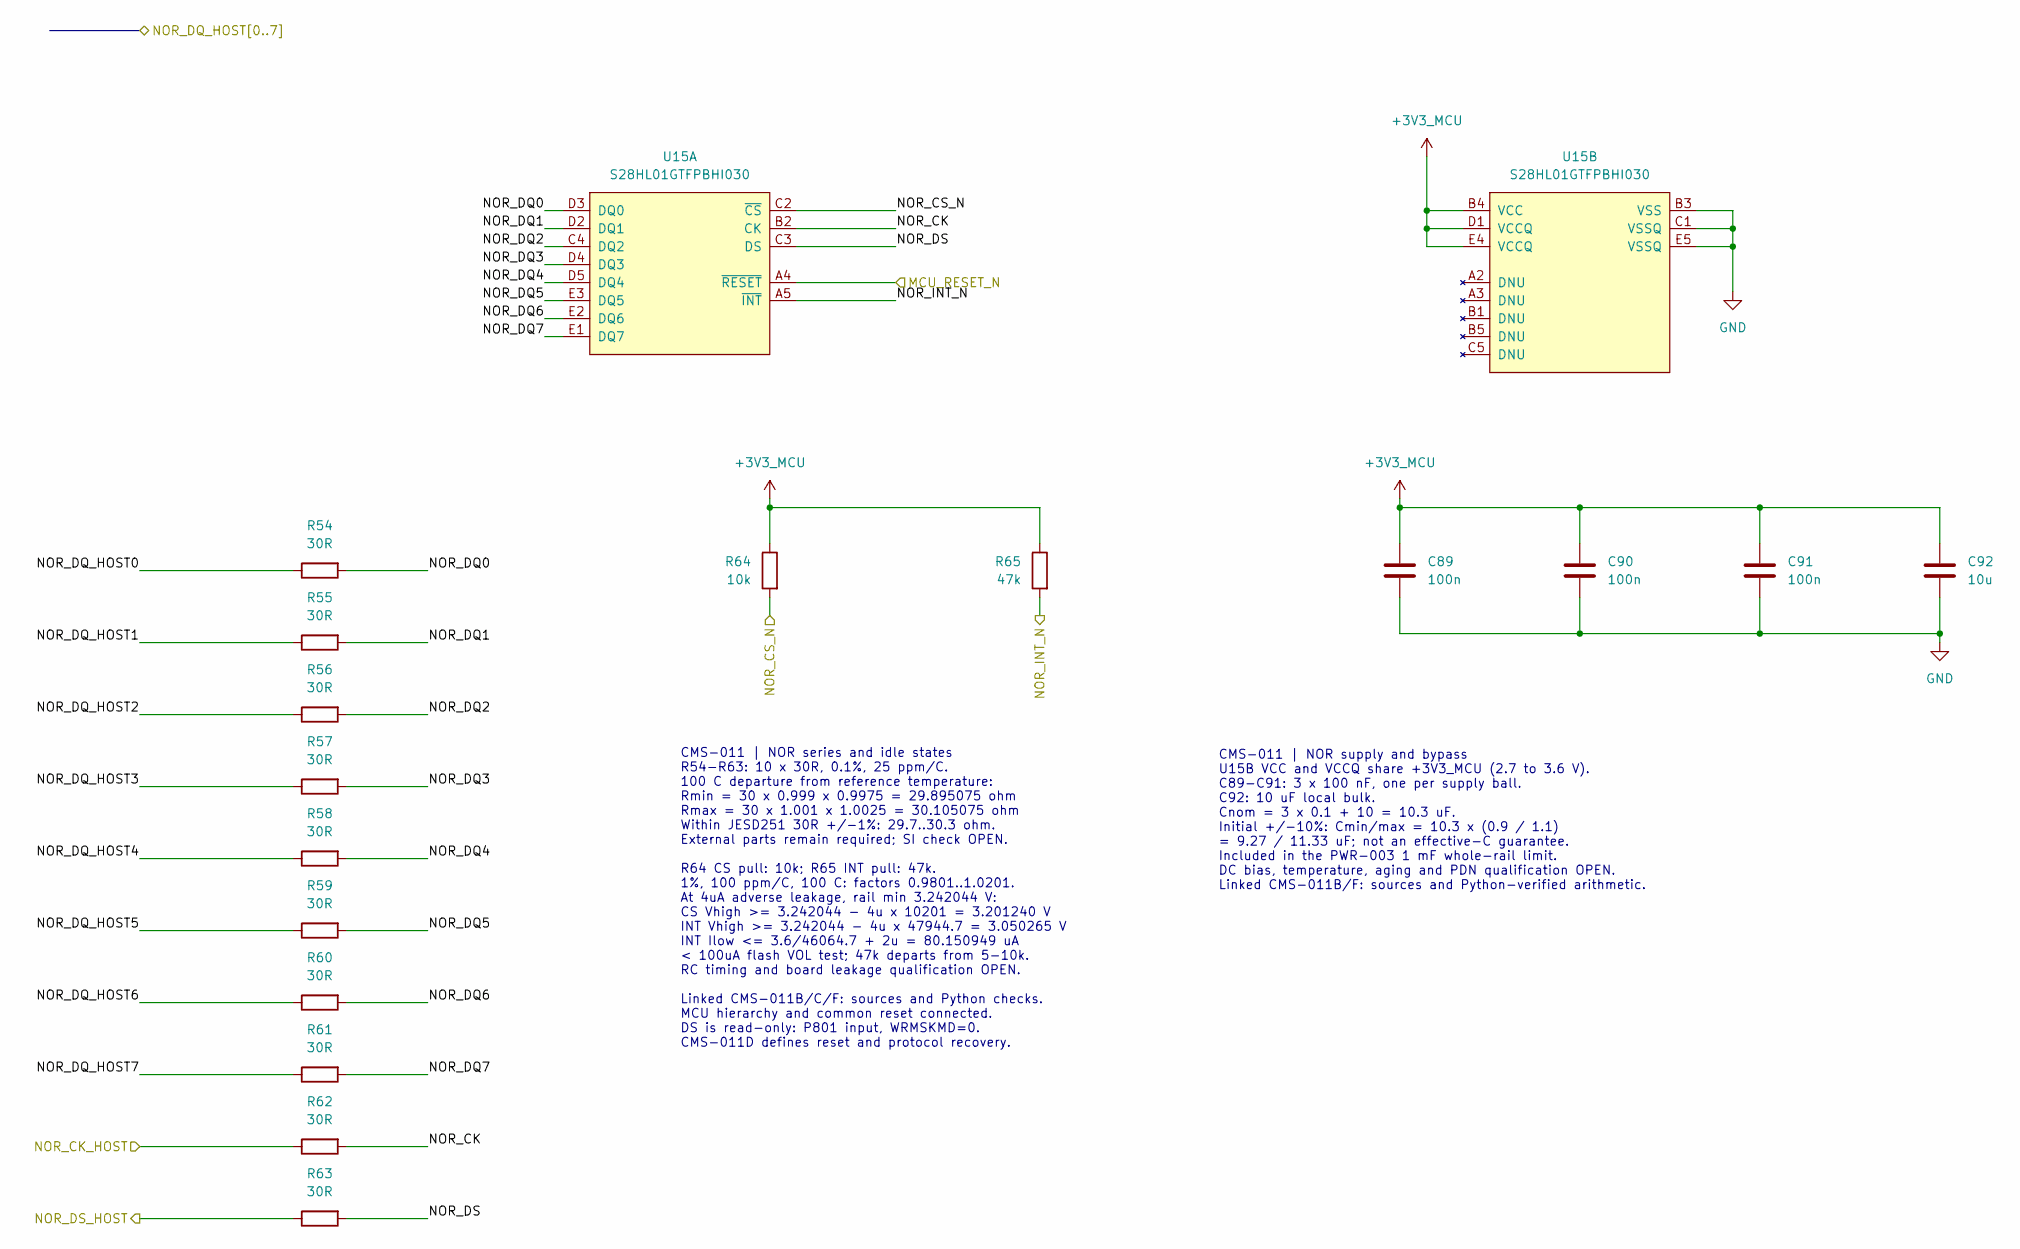
[picture p40: schematic nor_flash.kicad_sch]

Parts:
C89, C90, C91: 100n; Manufacturer_Part_Number C1608X7R1H104K080AA; DigiKey_Part_Number 445-1314-1-ND
C92: 10u; Manufacturer_Part_Number C3216X7R1V106K160AC; DigiKey_Part_Number 445-14799-1-ND
R54, R55, R56, R57, R58, R59, R60, R61, R62, R63: 30R; Manufacturer_Part_Number RT0603BRD0730RL; DigiKey_Part_Number 13-RT0603BRD0730RLCT-ND
R64: 10k; Manufacturer_Part_Number RC0603FR-0710KL; DigiKey_Part_Number 311-10.0KHRCT-ND
R65: 47k; Manufacturer_Part_Number RC0603FR-0747KL; DigiKey_Part_Number 311-47.0KHRCT-ND
U15: S28HL01GTFPBHI030; Manufacturer_Part_Number S28HL01GTFPBHI030; DigiKey_Part_Number 448-S28HL01GTFPBHI030-ND

Connections:
+3V3_MCU: C89.1, C90.1, C91.1, C92.1, R64.1, R65.1, U15.B4 (VCC), U15.D1 (VCCQ), U15.E4 (VCCQ)
GND: C89.2, C90.2, C91.2, C92.2, U15.B3 (VSS), U15.C1 (VSSQ), U15.E5 (VSSQ)
MCU_RESET_N: U15.A4 (~RESET)
NOR_CK: R62.2, U15.B2 (CK)
NOR_CK_HOST: R62.1
NOR_CS_N: R64.2, U15.C2 (~CS)
NOR_DQ0: R54.2, U15.D3 (DQ0)
NOR_DQ1: R55.2, U15.D2 (DQ1)
NOR_DQ2: R56.2, U15.C4 (DQ2)
NOR_DQ3: R57.2, U15.D4 (DQ3)
NOR_DQ4: R58.2, U15.D5 (DQ4)
NOR_DQ5: R59.2, U15.E3 (DQ5)
NOR_DQ6: R60.2, U15.E2 (DQ6)
NOR_DQ7: R61.2, U15.E1 (DQ7)
NOR_DQ_HOST0: R54.1
NOR_DQ_HOST1: R55.1
NOR_DQ_HOST2: R56.1
NOR_DQ_HOST3: R57.1
NOR_DQ_HOST4: R58.1
NOR_DQ_HOST5: R59.1
NOR_DQ_HOST6: R60.1
NOR_DQ_HOST7: R61.1
NOR_DS: R63.2, U15.C3 (DS)
NOR_DS_HOST: R63.1
NOR_INT_N: R65.2, U15.A5 (~INT)

Notes on the sheet:
CMS-011 | NOR series and idle states R54-R63: 10 x 30R, 0.1%, 25 ppm/C. 100 C departure from reference temperature: Rmin = 30 x 0.999 x 0.9975 = 29.895075 ohm Rmax = 30 x 1.001 x 1.0025 = 30.105075 ohm Within JESD251 30R +/-1%: 29.7..30.3 ohm. External parts remain required; SI check OPEN. R64 CS p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
CMS-011 | NOR supply and bypass U15B VCC and VCCQ share +3V3_MCU (2.7 to 3.6 V). C89-C91: 3 x 100 nF, one per supply ball. C92: 10 uF local bulk. Cnom = 3 x 0.1 + 10 = 10.3 uF. Initial +/-10%: Cmin/max = 10.3 x (0.9 / 1.1) = 9.27 / 11.33 uF; not an effective-C guarantee. Included in the PWR-003 1 m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
