bsikar/ra8p1-ereader-kicad/sim/kicad/protection/protection.kicad_sch

## KiCad design sim/kicad/protection/protection.kicad_sch (2026-10-07)

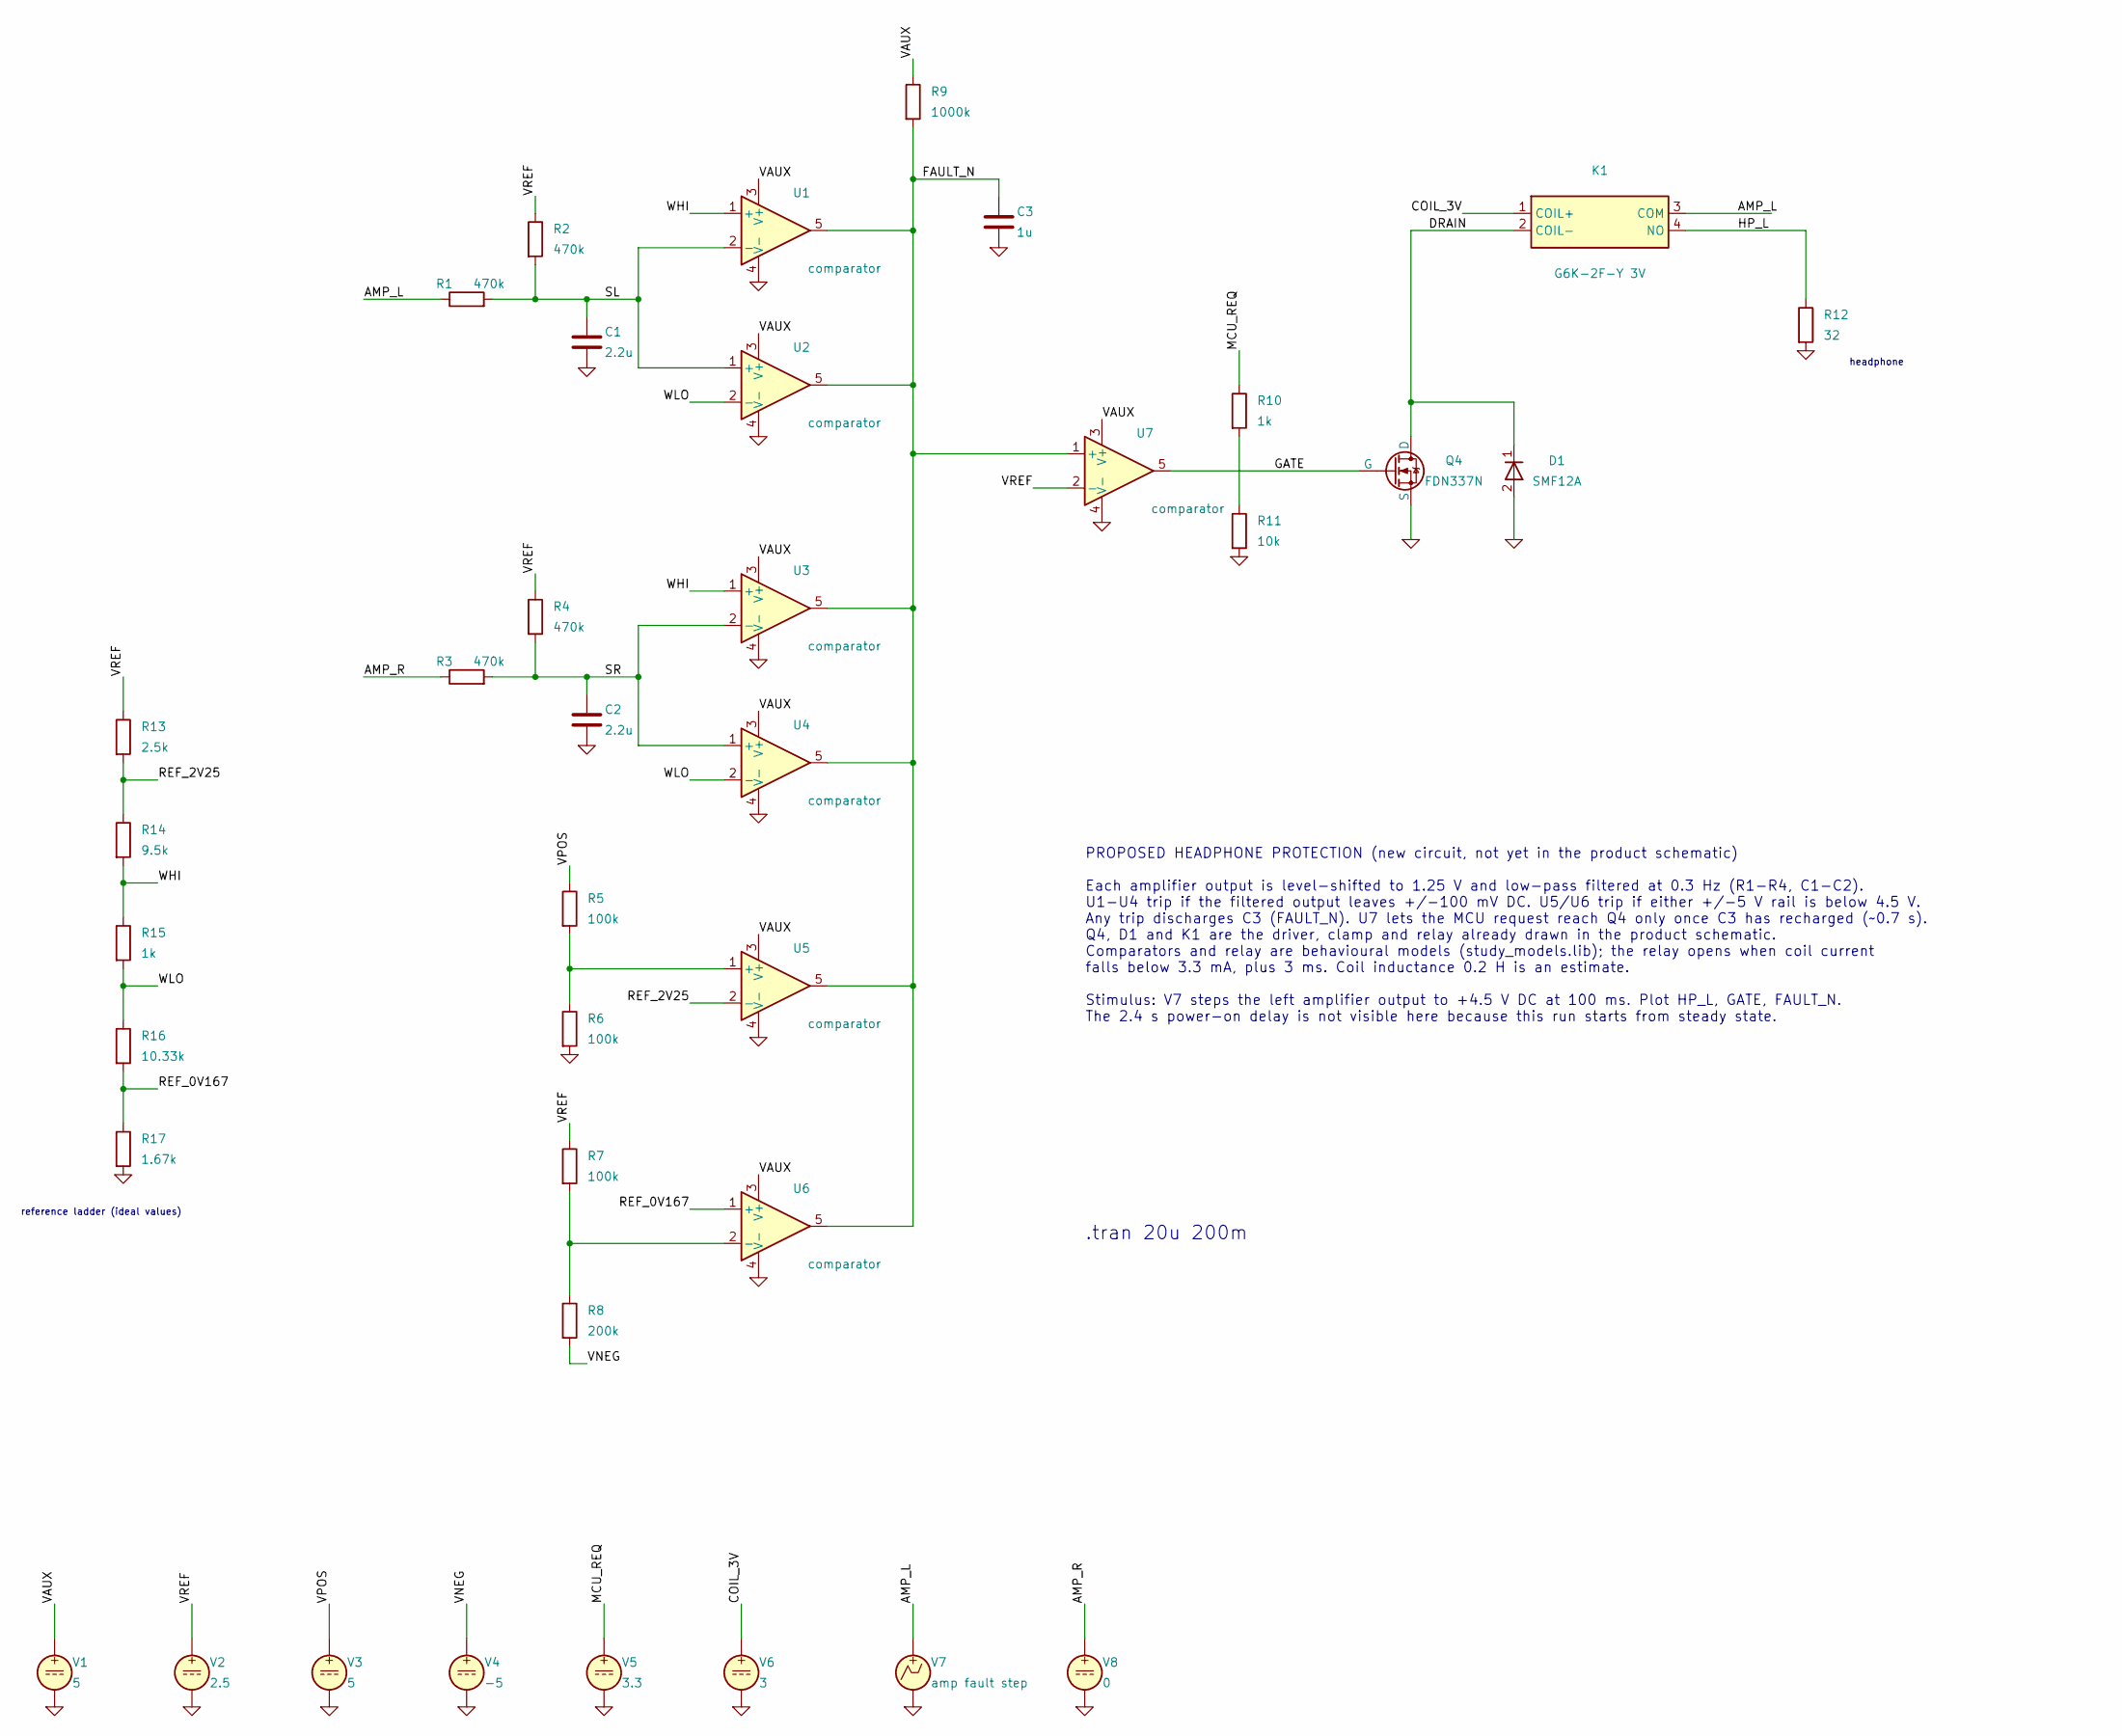
[picture p47: schematic protection.kicad_sch]

Parts:
C1, C2: 2.2u
C3: 1u
D1: SMF12A
K1: G6K-2F-Y 3V
Q4: FDN337N
R1, R2, R3, R4: 470k
R5, R6, R7: 100k
R8: 200k
R9: 1000k
R10, R15: 1k
R11: 10k
R12: 32
R13: 2.5k
R14: 9.5k
R16: 10.33k
R17: 1.67k
U1, U2, U3, U4, U5, U6, U7: comparator
V1, V3: 5
V2: 2.5
V4: -5
V5: 3.3
V6: 3
V7: amp fault step
V8: 0

Connections:
0: C1.2, C2.2, C3.2, D1.2 (A), Q4.3 (S), R6.2, R11.2, R12.2, R17.2, U1.4 (V-), U2.4 (V-), U3.4 (V-), U4.4 (V-), U5.4 (V-), U6.4 (V-), U7.4 (V-), V1.2, V2.2, V3.2, V4.2, V5.2, V6.2, V7.2, V8.2
AMP_L: K1.3 (COM), R1.1, V7.1
AMP_R: R3.1, V8.1
COIL_3V: K1.1 (COIL+), V6.1
DRAIN: D1.1 (K), K1.2 (COIL-), Q4.1 (D)
FAULT_N: C3.1, R9.2, U1.5, U2.5, U3.5, U4.5, U5.5, U6.5, U7.1 (+)
GATE: Q4.2 (G), U7.5
HP_L: K1.4 (NO), R12.1
MCU_REQ: R10.1, V5.1
unnamed: R5.2, R6.1, U5.1 (+)
unnamed: R7.2, R8.1, U6.2 (-)
unnamed: R10.2, R11.1
REF_0V167: R16.2, R17.1, U6.1 (+)
REF_2V25: R13.2, R14.1, U5.2 (-)
SL: C1.1, R1.2, R2.2, U1.2 (-), U2.1 (+)
SR: C2.1, R3.2, R4.2, U3.2 (-), U4.1 (+)
VAUX: R9.1, U1.3 (V+), U2.3 (V+), U3.3 (V+), U4.3 (V+), U5.3 (V+), U6.3 (V+), U7.3 (V+), V1.1
VNEG: R8.2, V4.1
VPOS: R5.1, V3.1
VREF: R2.1, R4.1, R7.1, R13.1, U7.2 (-), V2.1
WHI: R14.2, R15.1, U1.1 (+), U3.1 (+)
WLO: R15.2, R16.1, U2.2 (-), U4.2 (-)

Notes on the sheet:
reference ladder (ideal values)
headphone
.tran 20u 200m
PROPOSED HEADPHONE PROTECTION (new circuit, not yet in the product schematic) Each amplifier output is level-shifted to 1.25 V and low-pass filtered at 0.3 Hz (R1-R4, C1-C2). U1-U4 trip if the filtered output leaves +/-100 mV DC. U5/U6 trip if either +/-5 V rail is below 4.5 V. Any trip discharges 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
