bsikar/ra8p1-ereader-kicad/sim/kicad/quiet_chain/quiet_chain.kicad_sch

## KiCad design sim/kicad/quiet_chain/quiet_chain.kicad_sch (2026-10-07)

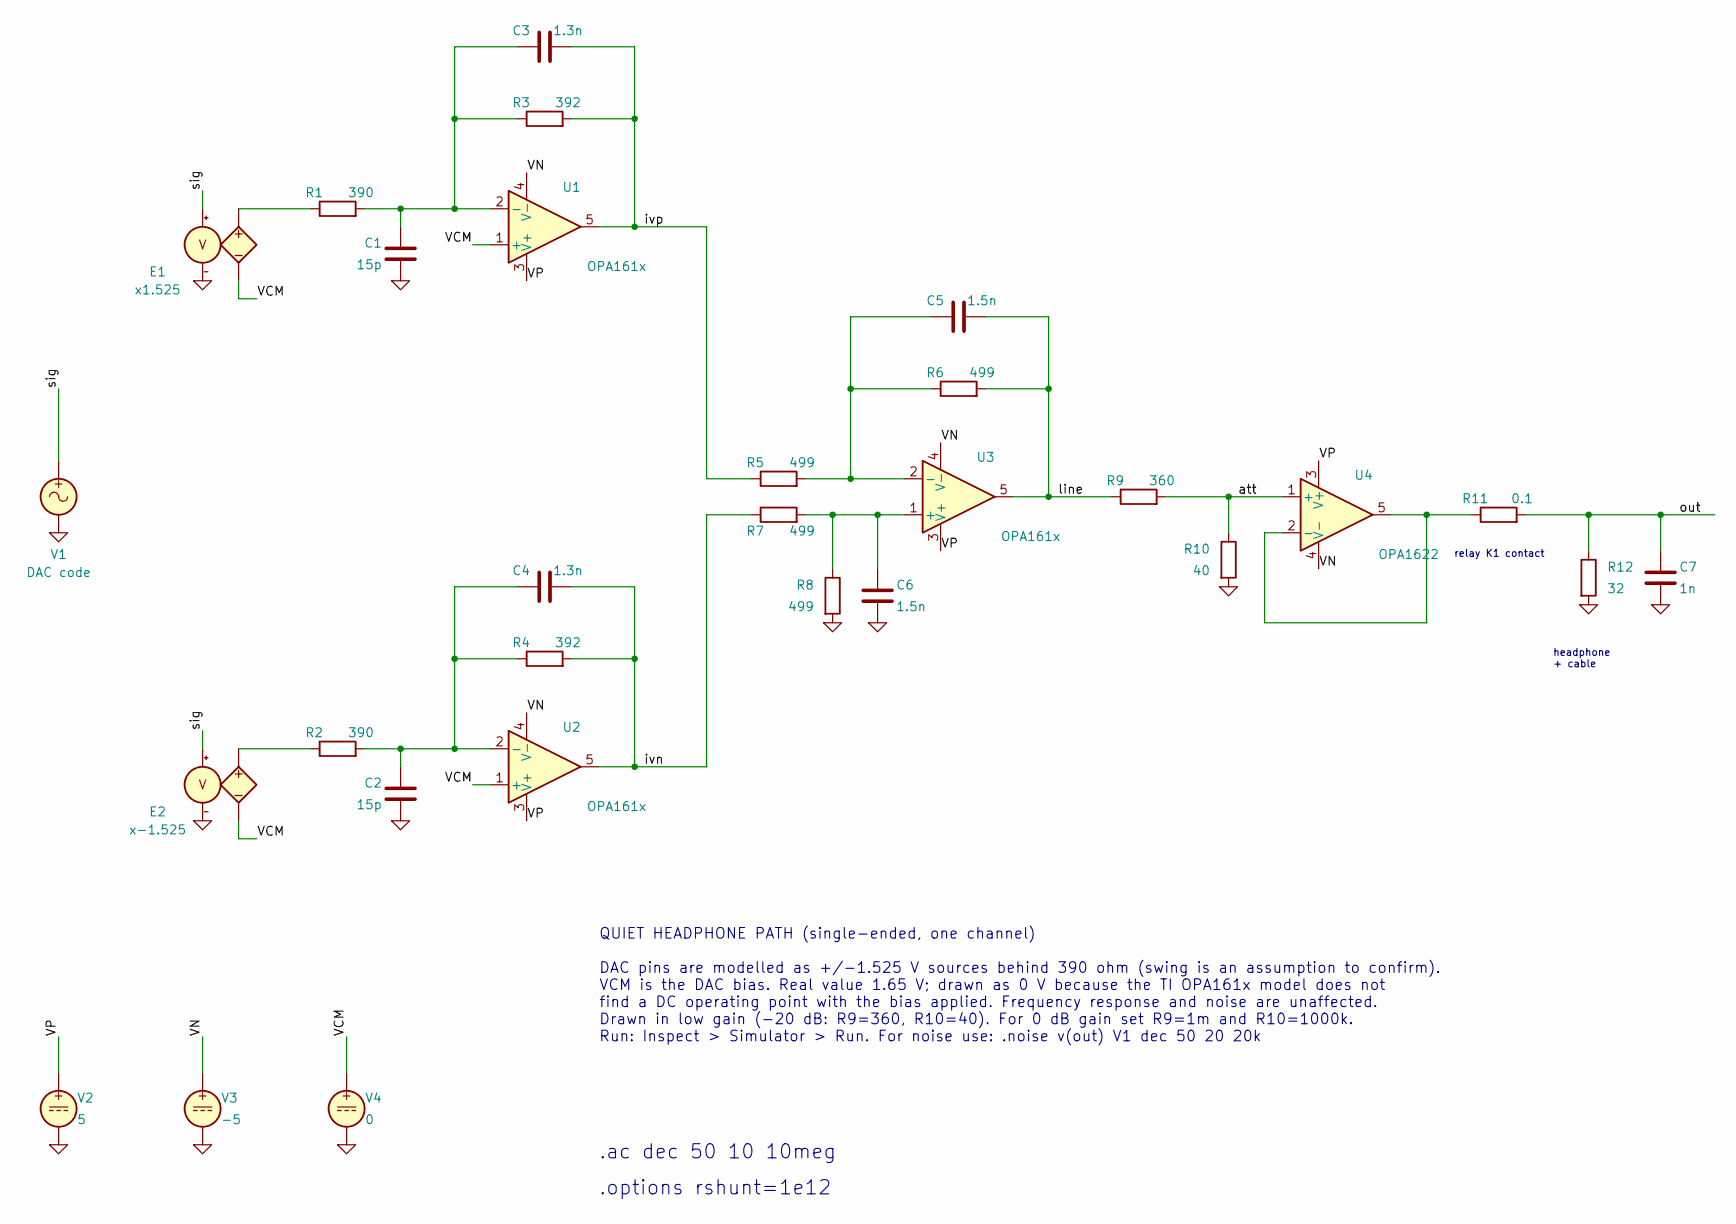
[picture p48: schematic quiet_chain.kicad_sch]

Parts:
C1, C2: 15p
C3, C4: 1.3n
C5, C6: 1.5n
C7: 1n
E1: x1.525
E2: x-1.525
R1, R2: 390
R3, R4: 392
R5, R6, R7, R8: 499
R9: 360
R10: 40
R11: 0.1
R12: 32
U1, U2, U3: OPA161x
U4: OPA1622
V1: DAC code
V2: 5
V3: -5
V4: 0

Connections:
0: C1.2, C2.2, C6.2, C7.2, E1.4 (C-), E2.4 (C-), R8.2, R10.2, R12.2, V1.2, V2.2, V3.2, V4.2
unnamed: C1.1, C3.1, R1.2, R3.1, U1.2 (-)
unnamed: C2.1, C4.1, R2.2, R4.1, U2.2 (-)
unnamed: C5.1, R5.2, R6.1, U3.2 (-)
unnamed: C6.1, R7.2, R8.1, U3.1 (+)
unnamed: E1.1 (N+), R1.1
unnamed: E2.1 (N+), R2.1
unnamed: R11.1, U4.2 (-), U4.5
VCM: E1.2 (N-), E2.2 (N-), U1.1 (+), U2.1 (+), V4.1
VN: U1.4 (V-), U2.4 (V-), U3.4 (V-), U4.4 (V-), V3.1
VP: U1.3 (V+), U2.3 (V+), U3.3 (V+), U4.3 (V+), V2.1
att: R9.2, R10.1, U4.1 (+)
ivn: C4.2, R4.2, R7.1, U2.5
ivp: C3.2, R3.2, R5.1, U1.5
line: C5.2, R6.2, R9.1, U3.5
out: C7.1, R11.2, R12.1
sig: E1.3 (C+), E2.3 (C+), V1.1

Notes on the sheet:
QUIET HEADPHONE PATH (single-ended, one channel) DAC pins are modelled as +/-1.525 V sources behind 390 ohm (swing is an assumption to confirm). VCM is the DAC bias. Real value 1.65 V; drawn as 0 V because the TI OPA161x model does not find a DC operating point with the bias applied. Frequency resp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
.ac dec 50 10 10meg
.options rshunt=1e12
relay K1 contact
headphone + cable
